AdamKeher/XCopyStandalone/esp8266/data/images/AK74.png

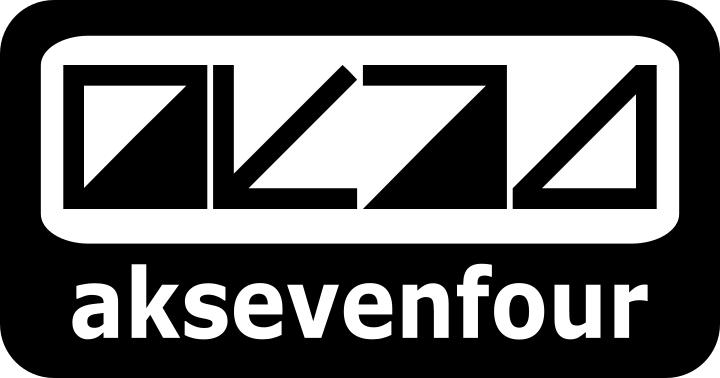
esp8266/data/images/AK74.png
