AdamKeher/XCopyStandalone/esp8266/data/images/AK74_white.png

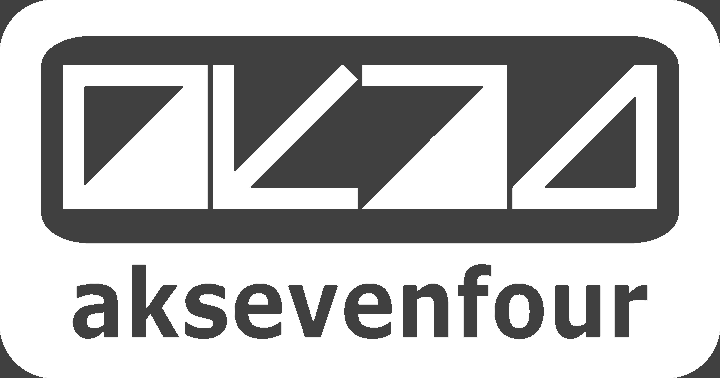
esp8266/data/images/AK74_white.png
