AdamKeher/XCopyStandalone/files/Graphics/mutation.bmp

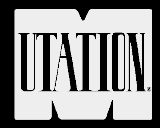
files/Graphics/mutation.bmp
