AdamKeher/XCopyStandalone/files/Graphics/sysinfo.bmp

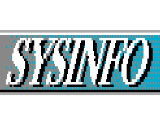
files/Graphics/sysinfo.bmp
