AdamKeher/XCopyStandalone/files/Graphics/XCopy Board.png

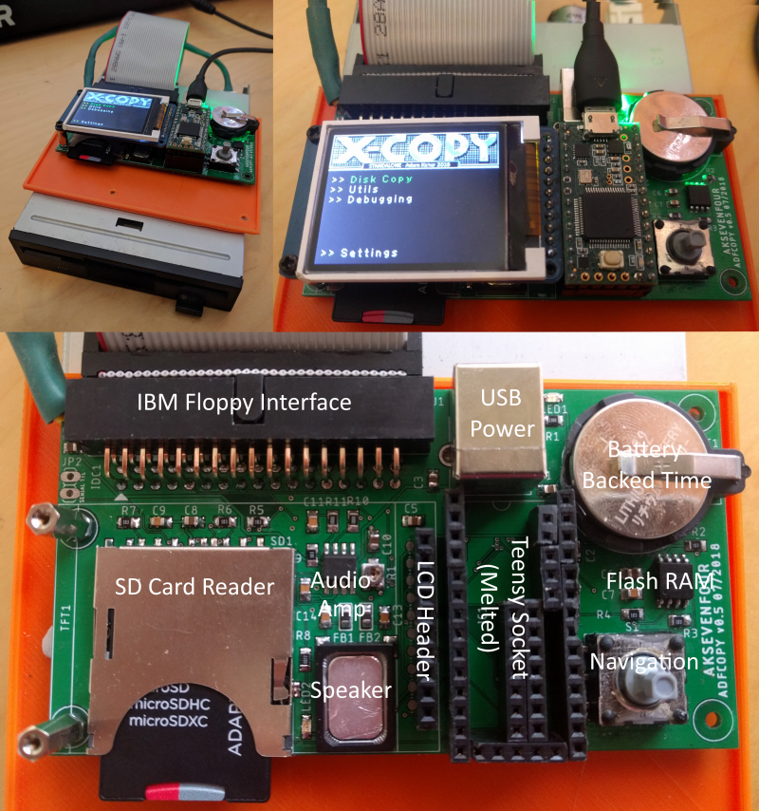
files/Graphics/XCopy Board.png
