AdamKeher/XCopyStandalone/src/XCopy/XCopyDisk.cpp

#include "XCopyDisk.h"
#include "XCopyScratch.h"

// #define XCOPY_DEBUG 1

/**
 * @brief Initialise the object
 * 
 * @param  graphics pointer to XCopyGraphics object
 * @param  audio pointer to XCopyAudio object
 * @param  esp pointer to XCopyESP object
 */
void XCopyDisk::begin(XCopyGraphics *graphics, XCopyAudio *audio, XCopyESP8266 *esp, XCopyFloppy *floppy)
{
    _graphics = graphics;
    _audio = audio;
    _esp = esp;
    _floppy = floppy;

    _floppy->setupDrive();

    // setupDrive() is what malloc's the track buffer, so the scratch arena cannot be
    // offered to anyone before this point. See XCopyScratch.h for why the buffer is
    // shared rather than each caller keeping its own.
    XCopyScratch::attach(_floppy);
}

// UI

/**
 * @brief Wait for user to change the disk in the current floppy drive. 
 */
void XCopyDisk::changeDisk()
{
    _graphics->clearScreen();
    _graphics->drawText(0, 60, ST7735_YELLOW, "           Change Disk");
    _esp->setStatus("Change Disk");

    bool diskInserted = _floppy->diskChange();
    while (diskInserted)
    {
        if (_cancelOperation)
        {
            _graphics->drawText(0, 70, ST7735_RED, "            Cancelled");
            return;
        }
        diskInserted = _floppy->diskChange();
        delay(500);
    }

    _graphics->drawText(0, 60, ST7735_GREEN, "    Disk Ejected. Waiting", true);
    _esp->setStatus("Disk Ejected. Waiting ...");

    diskInserted = _floppy->diskChange();
    while (!diskInserted)
    {
        if (_cancelOperation)
        {
            _graphics->drawText(0, 70, ST7735_RED, "            Cancelled");
            _esp->setStatus("Cancelled");
            return;
        }
        diskInserted = _floppy->diskChange();
        delay(3000);
    }
}

/**
 * @brief Draw disk flux on TFT and WebUI interfaces
 * 
 * @param trackNum track number of flux data
 * @param scale scale value flux values for drawing on TFT screen
 * @param yoffset y offset for drawing on TFT screen
 * @param updateWebUI bool value to determine if WebUI is updated
 */
void XCopyDisk::drawFlux(uint8_t trackNum, uint8_t scale, uint8_t yoffset, bool updateWebUI)
{
    // web interface
    // Static, and appended to in place below, so this buffer is allocated once
    // for the life of the program. Building it locally meant a ~1KB alloc/free
    // per track plus a realloc per concatenation, all inside the few KB left
    // between the stream buffer and the stack - which fragmented the heap until
    // the allocator wedged partway through the disk.
    static String data;
    data.reserve(1024);
    data.remove(0);
    for (int i = 0; i < 255; i++) {
        // concat() appends in place, so the reserve above holds. `data = data + x`
        // does not: it builds a StringSumHelper copy sized to len and assigns it
        // back, discarding the reserved capacity and reallocating every iteration.
        data.concat(_floppy->getHist()[i]);
        data.concat('|');
    }
    // Sent in pieces: concatenating these built another ~600 byte temporary
    // (plus intermediates) on top of the one we already hold, in the same
    // few KB left between the stream buffer and the stack.
    if (updateWebUI) {
        _esp->print("broadcast flux," + String(trackNum) + ",");
        _esp->print(data);
        _esp->print("\r\n");
    }

    // tft screen
    int scaled = 0;
    for (int i = 0; i < 255; i = i + scale)
    {
        // scale hist value
        for (int s = 0; s < scale; s++) { scaled += _floppy->getHist()[i + s]; }

        // draw hist
        if (scaled > 0)
        {
            scaled = (scaled / (32 * scale));
            scaled = scaled < 255 ? scaled : 255;
            float ratio = scaled / 255.0f;

            if (scaled < 5)
                _graphics->getTFT()->drawPixel(trackNum, yoffset, _graphics->LerpRGB(ST7735_WHITE, ST7735_YELLOW, ratio));
            else if (scaled < 50)
                _graphics->getTFT()->drawPixel(trackNum, yoffset, _graphics->LerpRGB(ST7735_YELLOW, ST7735_ORANGE, ratio));
            else
                _graphics->getTFT()->drawPixel(trackNum, yoffset, _graphics->LerpRGB(ST7735_ORANGE, ST7735_RED, ratio));
        }
        yoffset++;
    }
}

// File & Volume Names

/**
 * @brief Callback function used by SDfile::dateTimeCallback.
 *        Return today's date.
 * 
 * @param date date variable
 * @param time time variable
 */
void XCopyDisk::dateTime(uint16_t *date, uint16_t *time)
{
    // return date using FAT_DATE macro to format fields
    *date = FAT_DATE(year(), month(), day());

    // return time using FAT_TIME macro to format fields
    *time = FAT_TIME(hour(), minute(), second());
}

/**
 * @brief Get volume name of ADF file
 * 
 * @param ADFFileName path of ADF file
 * @param Source indicates SDCard or Flash Memory source
 * 
 * @result volume name for ADF file, "NDOS" if the disk is not dos formatted
 */
String XCopyDisk::getADFVolumeName(String ADFFileName, ADFFileSource source)
{
    _esp->setStatus("Geting Disk Name");

    String volumeName;
    volumeName = "NDOS";

    if (ADFFileName == "")
        return ">> File Error";

    // Zeroed: an unrecognised source would otherwise run the root block checks below
    // over stack garbage. All-zero fails them and yields "NDOS".
    byte trackBuffer[512];
    memset(trackBuffer, 0, sizeof(trackBuffer));

    if (source == _sdCard)
    {
        XCopySDCard _sdcard;

        // Was `if (_sdcard.begin())`, which reported an error when the card
        // initialised and carried on when it did not. begin() returns true on
        // success.
        if (!_sdcard.begin()) {
            return ">> SD Error";
        }

        File ADFFile;
        ADFFile.open(ADFFileName.c_str(), FILE_READ);

        if (!ADFFile) {
            return ">> File Error";
        }

        ADFFile.seek(40 * 2 * 11 * 512);
        ADFFile.read(trackBuffer, sizeof(trackBuffer));
        ADFFile.close();
    }
    else if (source == _flashMemory) {
        if (!SerialFlash.begin(PIN_FLASHCS)) { return ">> Flash Error"; }

        SerialFlashFile ADFFile = SerialFlash.open(ADFFileName.c_str());

        if (!ADFFile) { return ">> File Error"; }

        ADFFile.seek(40 * 2 * 11 * 512);
        ADFFile.read(trackBuffer, sizeof(trackBuffer));
        ADFFile.close();
    }

    int nameLen = trackBuffer[432];
    if (nameLen > 30) { return "NDOS"; }
    int temp = 0;
    for (int i = 0x04; i < 0x0c; i++) {
        temp += trackBuffer[i];
    }
    for (int i = 0x10; i < 0x14; i++) {
        temp += trackBuffer[i];
    }
    for (int i = 463; i < 472; i++) {
        temp += trackBuffer[i];
    }
    for (int i = 496; i < 504; i++) {
        temp += trackBuffer[i];
    }
    if (temp != 0) { return "NDOS"; }
    for (int i = 0; i < 4; i++) {
        temp += trackBuffer[i];
    }
    if (temp != 2) { return "NDOS"; }
    temp = 0;
    for (int i = 508; i < 512; i++) {
        temp += trackBuffer[i];
    }
    if (temp != 1) { return "NDOS"; }
    volumeName = "";
    for (int i = 0; i < nameLen; i++) {
        volumeName += (char)trackBuffer[433 + i];
    }

    return volumeName;
}

/**
 * @brief Generated ADF filename in format: /<SD_ADF_PATH>/<DATETIME> <DISKNAME>.adf
 * 
 * @param diskname diskname used in ADF filename
 * 
 * @result generated ADF file name
 */
String XCopyDisk::generateADFFileName(String diskname) {
    String path = String(SD_ADF_PATH);
    char dtBuffer[32];
    sprintf(dtBuffer, "%04d%02d%02d %02d%02d", year(), month(), day(), hour(), minute());
    String datetime = String(dtBuffer);
    return "/" + path + "/" + datetime + " " + diskname + ".adf";
}

// Cancel

/**
 * @brief Cancel running operation
 */
void XCopyDisk::cancelOperation() {
    _cancelOperation = true;
}

/**
 * @brief Used to update TFT and WebUI interface when operation is cancelled.
 *        If specificed, unprocessed tracks will be highlighted red.
 * 
 * @param trackNum logical track number operation was canceled on. -1 if not needed.
 */
void XCopyDisk::OperationCancelled(uint8_t trackNum) {
    _graphics->drawText(0, 10, ST7735_RED, "Operation Cancelled", true);
    if (trackNum >= 0)
    {
        _graphics->drawDisk(trackNum, ST7735_RED);
        _esp->sendWebSocket("resetTracks,red," + String(trackNum));
        _trackMap.setRange(trackNum, trackSkipped);
    }
    // Released before logging - anything printed while the map owns the console
    // scrolls the table out from under the cursor addressing.
    _trackMap.end("CANCELLED");
    Log << XCopyConsole::error("Operation Cancelled") << "\r\n";
    _audio->playBong(false);
}

// Read & Write tracks

/**
 * @brief Reads specified track into track buffer
 * 
 * @param trackNum logical track number to read
 * @param verify flags if this read is being use in a verify operation
 * @param retryCount number of retries when reading disk
 * @param silent output flag
 * 
 * @result number of retries required to read track. -1 is error. 
 */
int XCopyDisk::readDiskTrack(uint8_t trackNum, bool verify, uint8_t retryCount, bool silent) {
    // white = seek
    // green = OK - no retries
    // yellow = ~OK - quick retry required
    // orange = ~OK - retry required
    // red = ERROR - track did not read correctly
    // return 0 = OK, -1 = ERROR, >0 = OK w/ RETRY Count

    int retries = 0;
    int readResult = -1;

    while (readResult == -1 && retries < retryCount) {
        // read track
        if (!silent) _graphics->drawTrack(trackNum / 2, trackNum % 2, true, false, 0, verify, ST7735_WHITE);
        if (!silent) _trackMap.setTrack(trackNum, trackBusy, 0, verify);
        _esp->setTrack(trackNum, "white", verify ? "V" : "");
        _floppy->gotoLogicTrack(trackNum);
        readResult = _floppy->readTrack(true);

        if (readResult != -1) {
            // read OK
            if (_floppy->getWeakTrack() > 0) {
                if (!silent) _graphics->drawTrack(trackNum / 2, trackNum % 2, true, false, 0, verify, ST7735_YELLOW);
                if (!silent) _trackMap.setTrack(trackNum, trackWeak, 0, verify);
                _esp->setTrack(trackNum, "yellow", verify ? "V" : "");
            }
            else {
                if (!silent) _graphics->drawTrack(trackNum / 2, trackNum % 2, true, false, 0, verify, ST7735_GREEN);
                if (!silent) _trackMap.setTrack(trackNum, trackOK, 0, verify);
                _esp->setTrack(trackNum, "green", verify ? "V" : "");
            }
        }
        else {
            // read error
            if (!silent) _graphics->drawTrack(trackNum / 2, trackNum % 2, true, false, 0, verify, ST7735_RED);            
            if (!silent) _trackMap.setTrack(trackNum, trackError, retries + 1, verify);
            _esp->setTrack(trackNum, "red", verify ? "V" : String(retries + 1));
            retries++;
            _audio->playBong(false);
            delay(1000);
        }

        if (_cancelOperation) { return -1; }
    }

    if (readResult == 0 && retries > 0) {
        if (!silent) _graphics->drawTrack(trackNum / 2, trackNum % 2, true, false, 0, verify, ST7735_ORANGE);
        if (!silent) _trackMap.setTrack(trackNum, trackRetried, retries, verify);
        _esp->setTrack(trackNum, "orange", verify ? "V" : String(retries));
    }

    return readResult == -1 ? readResult : retries;
}

/**
 * @brief Write specified track from track buffer
 * 
 * @param trackNum logical track number to write
 * @param retryCount number of retries when writing track
 * 
 * @result number of retries required to write track. -1 is error. 
 */
int XCopyDisk::writeDiskTrack(uint8_t trackNum, uint8_t retryCount)
{
    // white = seek
    // green = OK
    // orange = ~OK - retry required
    // red = ERROR - track did not write correctly
    // return: 0+ = OK, -1 = ERROR

    int retries = 0;
    int writeResult = -1;

    while (writeResult == -1 && retries < retryCount) {
        // write track
        _graphics->drawTrack(trackNum / 2, trackNum % 2, true, false, 0, false, ST7735_WHITE);
        _trackMap.setTrack(trackNum, trackBusy);
        _esp->setTrack(trackNum, "white");
        _floppy->gotoLogicTrack(trackNum);    
        writeResult = _floppy->writeTrack(); // returns 0 = OK, -1 = ERROR

        if (writeResult == 0) {
            // write OK
            if (retries == 0) {
                // write OK w/ no retries
                _graphics->drawTrack(trackNum / 2, trackNum % 2, true, false, 0, false, ST7735_GREEN);
                _trackMap.setTrack(trackNum, trackOK);
                _esp->setTrack(trackNum, "green");
            }
            else {
                // write OK w/ retries
                _graphics->drawTrack(trackNum / 2, trackNum % 2, true, false, 0, false, ST7735_ORANGE);
                _trackMap.setTrack(trackNum, trackRetried, retries + 1);
                _esp->setTrack(trackNum, "orange", String(retries + 1));
            }
        }
        else {
            // write error
            _graphics->drawTrack(trackNum / 2, trackNum % 2, true, true, retries + 1, false, ST7735_RED);
            _trackMap.setTrack(trackNum, trackError, retries + 1);
            _esp->setTrack(trackNum, "red", String(retries + 1));
            // The map already carries the failing track and the attempt number;
            // printing here as well would scroll the table out from under it.
            if (!_trackMap.active()) Serial << "Write failed! - Try: " << retries + 1 << "\r\n";
            retries++;
            _audio->playBong(false);
            delay(1000);
        }        

        if (_cancelOperation) { return -1; }
    }

    return writeResult == -1 ? writeResult : retries;
}

// ADF Disk

/**
 * @brief Copy floppy disk to ADF file on SDCard or Flash
 * 
 * @param ADFFileName path of ADF file on SDCard, if blank and destination is SDCard, the name will be autogenerated
 * @param verify verify tracks by reading track a second time and compairing it to the data written
 * @param retryCount number of retries when reading track
 * @param destination indicates SDCard or Flash Memory destination
 * @param setEsp set mode and state for WebUI
 * 
 * @result success or failure of copy process
 * 
 * @todo TODO: Create XCopyLogFile object? Move CRC code into function. 
 */
bool XCopyDisk::diskToADF(String ADFFileName, bool verify, uint8_t retryCount, ADFFileSource destination, bool setEsp) {
    FastCRC32 CRC32;
    FastCRC16 CRC16;
    uint32_t disk_crc32 = 0;
    uint16_t track_crc16 = 0;
    _cancelOperation = false;
    String statusText = "";
    String diskName = "";

    int readErrors = 0;
    int weakTracks = 0;
    int totalReadErrors = 0;
    int totalWeakTracks = 0;
    
    File ADFFile;
    File ADFLogFile;
    SerialFlashFile ADFFlashFile;

    // setup TFT and WebUI
    _graphics->bmpDraw("XCPYLOGO.BMP", 0, 87);
    _graphics->drawDiskName("");
    _graphics->drawDisk();

    // dont update the mode and state for functions such as Disk to Disk
    if (setEsp) {
        _esp->setMode(destination == _sdCard ? "Copy Disk to ADF" : "Copy Disk to Flash");
        _esp->setState(destination == _sdCard ? copyDiskToADF : copyDiskToFlash);
    }
    _esp->resetDisk();
    _esp->setTab("diskcopy");

    // check if disk is present in floppy
    if (!_floppy->diskChange()) {
        _graphics->drawText(0, 10, ST7735_RED, "No Disk Inserted");
        Log << XCopyConsole::error("No Disk Inserted") << "\r\n";
        _esp->setStatus("No disk inserted");
        _audio->playBong(false);
        return false;
    }

    // get and set diskname
    diskName = _floppy->getName();
    _graphics->drawDiskName(diskName);
    _esp->setDiskName(diskName);

    // get filesnames
    String fullPath = ADFFileName == "" ? generateADFFileName(diskName) : ADFFileName;
    String logfileName = fullPath.substring(0, fullPath.length() - 4).append(".log");

    // set status on WebUI
    statusText = String("Copying floppy disk to ").append(destination == _sdCard ? "'"+ fullPath +"' on SD card" : "flash memory");   
    _esp->setStatus(statusText);

    // Open SD File or SerialFile
    XCopySDCard _sdcard;
    if (destination == _sdCard) {
        // card detect
        if (!_sdcard.cardDetect()) {
            _graphics->drawText(0, 10, ST7735_RED, "No SDCard detected");
            Log << XCopyConsole::error("No SDCard detected") << "\r\n";
            _esp->setStatus("SD card not inserted");
            _audio->playBong(false);
            return false;
        }

        // init
        if (!_sdcard.begin()) {
            _graphics->drawText(0, 10, ST7735_RED, "SD Init Failed");
            Log << XCopyConsole::error("SD Init Failed") << "\r\n";
            _esp->setStatus("SD card initialisation failed");
            _audio->playBong(false);
            return false;
        }

        // make ADF path
        if (!_sdcard.fileExists(SD_ADF_PATH)) _sdcard.makeDirectory(SD_ADF_PATH);

        // remove sdcard adf & log files if they exist
        if (_sdcard.fileExists(fullPath)) _sdcard.deleteFile(fullPath.c_str());
        if (_sdcard.fileExists(logfileName)) _sdcard.deleteFile(logfileName.c_str());

        // open sdcard files
        SdFile::dateTimeCallback(dateTime);
        ADFFile = _sdcard.getSdFat().open(fullPath.c_str(), FILE_WRITE);
        ADFLogFile = _sdcard.getSdFat().open(logfileName.c_str(), FILE_WRITE);
        SdFile::dateTimeCallbackCancel();

        // if adf file failed top open
        if (!ADFFile) {
            ADFFile.close();
            ADFLogFile.close();
            _graphics->drawText(0, 10, ST7735_RED, "SD ADF File Open Failed");
            Log << XCopyConsole::error("SD ADF File Open Failed") << "\r\n";
            _esp->setStatus("File '" + ADFFileName + "' failed to open on the SD card");
            _audio->playBong(false);
            return false;
        }

        // if log file failed to open
        if (!ADFLogFile) {
            ADFFile.close();
            ADFLogFile.close();
            _graphics->drawText(0, 10, ST7735_RED, "SD Log File Open Failed");
            Log << XCopyConsole::error("SD Log File Open Failed") << "\r\n";
            _esp->setStatus("File '" + logfileName + "' failed to open on the SD card");
            _audio->playBong(false);
            return false;
        }

        // create log file header
        ADFLogFile.println("{");
        ADFLogFile.println("\t\"volume\": \"" + diskName + "\",");
        char buffer[256];
        sprintf(buffer, "%04d-%02d-%02d %02d:%02d:%02d", year(), month(), day(), hour(), minute(), second());
        ADFLogFile.println("\t\"date\": \"" + String(buffer) + "\",");
        ADFLogFile.println("\t\"origin\": \"XCopy Standalone\",");
        ADFLogFile.println("\t\"timestamp\": " + String(now()) + ",");
        ADFLogFile.println("\t\"tracks\": [");
    }
    else if (destination == _flashMemory) {
        if (!SerialFlash.begin(PIN_FLASHCS)) {
            _graphics->drawText(0, 10, ST7735_RED, "Serial Flash Init Failed");
            Log << XCopyConsole::error("Serial Flash Init Failed") << "\r\n";
            _esp->setStatus("Onboard serial Flash failed to initialise");
            _audio->playBong(false);
            return false;
        }

        ADFFlashFile = SerialFlash.open(ADFFileName.c_str());

        _graphics->drawText(0, 10, ST7735_ORANGE, "Erasing Flash...", true);
        _esp->setStatus("Erasing Flash ...");

        ADFFlashFile.erase();

        while (!SerialFlash.ready()) { }

        _graphics->drawText("Done");
        _esp->setStatus("Erasing Flash ... Done");

        ADFFlashFile = SerialFlash.open(ADFFileName.c_str());
        if (!ADFFlashFile) {
            ADFFlashFile.close();
            _graphics->drawText(0, 10, ST7735_RED, "Serial Flash File Open Failed", true);
            Log << XCopyConsole::error("Serial Flash File Open Failed") << "\r\n";
            _esp->setStatus("Serial flash file failed to open");
            _audio->playBong(false);
            return false;
        }

        ADFFlashFile.seek(0);
    }

    // clear XCopy logo for flux
    _graphics->getTFT()->fillRect(0, 85, _graphics->getTFT()->width(), _graphics->getTFT()->height()-85, ST7735_BLACK);
    _graphics->getTFT()->drawFastHLine(0, 85, _graphics->getTFT()->width(), ST7735_GREEN);

    _trackMap.begin(destination == _sdCard ? "READ DISK TO ADF" : "READ DISK TO FLASH", diskName);

    // MD5 setup
    MD5_CTX ctx;
    MD5::MD5Init(&ctx);

    // YELLOW = Begin, GREEN = Read OK, ORANGE = Read after Retries, RED = Read Error, MAGENTA = Verify Error
    for (int trackNum = 0; trackNum < 160; trackNum++) {
        if (_cancelOperation) {
            OperationCancelled(trackNum);
            ADFLogFile.println("\r\nCancelled.");
            ADFLogFile.close();
            ADFFile.close();
            return false;
        }

        // read track
        int readResult = readDiskTrack(trackNum, false, retryCount);

        // draw flux
        _floppy->analyseHist(true);
        drawFlux(trackNum, 6, 85);

        if (_floppy->getWeakTrack()) {
            weakTracks += _floppy->getWeakTrack();
            totalWeakTracks++;
        }

        if (readResult != 0) {
            // if there has been error on either side, set error for whole cylinder else increment retry count
            if (readErrors == -1 || readResult == -1)
                readErrors = -1;
            else
                readErrors += readResult;
            totalReadErrors++;
        }

        // calculate CRC
        if (destination == _sdCard) {
            uint8_t side = trackNum % 2;

            for (int sec = 0; sec < 11; sec++) {
                struct Sector *aSec = (Sector *)&_floppy->getTrack()[sec].sector;

                // total disk CRC
                if (sec == 0 && trackNum == 0)
                    disk_crc32 = CRC32.crc32(aSec->data, sizeof(aSec->data));
                else
                    disk_crc32 = CRC32.crc32_upd(aSec->data, sizeof(aSec->data));

                // cyl CRC16
                if (sec == 0 && side == 0) {
                    // Serial << "trackNum: " << trackNum << " Side: " << side << " Sec: " << sec << " CCITT\r\n";
                    track_crc16 = CRC16.ccitt(aSec->data, sizeof(aSec->data));
                }
                else {
                    // Serial << "trackNum: " << trackNum << " Side: " << side << " Sec: " << sec << " CCITT_UPD\r\n";
                    track_crc16 = CRC16.ccitt_upd(aSec->data, sizeof(aSec->data));
                }
            }

            if (side == 1) {
                uint8_t cylinder = (trackNum - 1) / 2;
                ADFLogFile.print("\t\t{ \"track\": " + String(cylinder) + ", \"crc16\": \"0x");
                ADFLogFile.print(track_crc16, HEX);
                ADFLogFile.print("\", \"retries\": " + String(readErrors) + ", \"weak\": " + String(weakTracks) + " }");
                ADFLogFile.println(cylinder != 79 ? "," : "");

                weakTracks = 0;
                readErrors = 0;
            }
        }

        // write track (11 sectors per track)
        for (int i = 0; i < 11; i++) {
            const struct Sector *aSec = (Sector *)&_floppy->getTrack()[i].sector;
            // calculate MD5
            MD5::MD5Update(&ctx, aSec->data, 512);
            if (destination == _sdCard) {
                ADFFile.write(aSec->data, 512);
            }
            else if (destination == _flashMemory) {
                ADFFlashFile.write(aSec->data, 512);
                ADFFlashFile.flush();
                while (!SerialFlash.ready()) { }
            }
        }

        // verify
        if (verify) {
            // reread track to compare to file
            readDiskTrack(trackNum, true, retryCount);

            bool compareError = false;
            char buffer[512];

            // move file pointer pack 1 track
            if (destination == _sdCard)
                ADFFile.seek(ADFFile.position() - 11 * 512);
            else if (destination == _flashMemory)
                ADFFlashFile.seek(ADFFlashFile.position() - 11 * 512);

            // compare sectors to file
            for (int i = 0; i < 11; i++) {
                const struct Sector *aSec = (Sector *)&_floppy->getTrack()[i].sector;

                if (destination == _sdCard)
                    ADFFile.read(buffer, sizeof(buffer));
                else if (destination == _flashMemory)
                    ADFFlashFile.read(buffer, sizeof(buffer));

                if (memcmp(aSec->data, buffer, 512))
                    compareError = true;
            }

            if (compareError) {
                _graphics->drawTrack(trackNum / 2, trackNum % 2, true, false, 0, true, ST7735_MAGENTA);
                _trackMap.setTrack(trackNum, trackVerifyError, 0, true);
                _esp->setTrack(trackNum, "magenta,");
                _audio->playBong(false);
            }
            else {
                _graphics->drawTrack(trackNum / 2, trackNum % 2, true, false, 0, true, ST7735_GREEN);
                _trackMap.setTrack(trackNum, trackOK, 0, true);
                _esp->setTrack(trackNum, "green");
            }
        }
    }

    String sMD5 = ctxToMD5(&ctx);

    _trackMap.end(String("COMPLETE - ") + totalReadErrors + " bad, " + totalWeakTracks + " weak of 160 tracks");
    Log << (totalReadErrors ? XCopyConsole::error("Read errors on " + String(totalReadErrors) + " track(s)")
                            : XCopyConsole::success("All 160 tracks read")) << "\r\n";
    Log << "MD5: " << sMD5 << "\r\n";

    if (destination == _sdCard) {
        ADFLogFile.println("\t],");
        ADFLogFile.println("\t\"readErrors\": " + String(totalReadErrors) + ",");
        ADFLogFile.println("\t\"weakTracks\": " + String(totalWeakTracks) + ",");
        ADFLogFile.print("\t\"crc32\": \"0x");
        ADFLogFile.print(disk_crc32, HEX);
        ADFLogFile.println("\",");
        ADFLogFile.println("\t\"md5\": \"" + sMD5 + "\"");
        ADFLogFile.println("}");
    }

    ADFFile.close();
    ADFLogFile.close();
    ADFFlashFile.close();
    _audio->playBoing(false);

    statusText = String("Completed copying floppy disk to ").append(destination == _sdCard ? "'<a href=\"/sdcard" + fullPath + "\">" + fullPath + "</a>' on SD card. <a target=\"_blank\" href=\"/sdcard" + logfileName  + "\">Log File</a> <i class=\"fa-solid fa-hashtag\"></i> MD5: " + sMD5 : "flash memory. <i class=\"fa-solid fa-hashtag\"></i> MD5: " + sMD5);
    _esp->setStatus(statusText);

    return true;
}

/**
 * @brief Generated SCP filename in format: /<SD_SCP_PATH>/<DATETIME> <DISKNAME>.scp
 *
 * @param diskname diskname used in SCP filename
 *
 * @result generated SCP file name
 */
String XCopyDisk::generateSCPFileName(String diskname) {
    String path = String(SD_SCP_PATH);
    char dtBuffer[32];
    sprintf(dtBuffer, "%04d%02d%02d %02d%02d", year(), month(), day(), hour(), minute());
    String datetime = String(dtBuffer);
    return "/" + path + "/" + datetime + " " + diskname + ".scp";
}

/**
 * @brief Captures one track of raw flux and streams it into an open SCP image.
 *
 * The counterpart of readDiskTrack() for flux, and it paints the same three surfaces
 * in the same order with the same colours. What it does not have is a notion of a
 * good or a bad read: there is nothing to checksum, so the only failure a capture can
 * detect is the SD card falling behind the drive, which fluxOverran() reports and a
 * retry fixes.
 *
 * @param trackNum logical track number, which is also the SCP track number
 * @param writer image to stream into, already positioned by the caller
 * @param revolutions revolutions to store
 * @param retryCount retries allowed before the track is abandoned
 *
 * @result number of retries required. -1 is error.
 */
int XCopyDisk::captureDiskTrack(uint8_t trackNum, XCopySCPWriter *writer,
                                uint8_t revolutions, uint8_t retryCount) {
    int retries = 0;

    // Held for the whole track, retries included, and released however this returns.
    // The ring is the MFM stream buffer; nothing may decode a track or run a transfer
    // until it is given back.
    XCopyScratch::Guard scratch("disk.captureDiskTrack", sizeof(uint16_t));
    if (!scratch.valid()) return -1;

    // A revolution is 200ms; the drive may need to spin up and the first index can be
    // a full revolution away. Generous, because the alternative to a timeout here is
    // hanging forever on a drive with no disk in it.
    const uint32_t captureTimeout = 2000 + ((uint32_t)revolutions * 400);

    while (retries <= retryCount) {
        _graphics->drawTrack(trackNum / 2, trackNum % 2, true, retries > 0, retries, false, ST7735_WHITE);
        _trackMap.setTrack(trackNum, trackBusy);
        _esp->setTrack(trackNum, "white", retries > 0 ? String(retries) : "");

        _floppy->gotoLogicTrack(trackNum);

        if (!writer->beginTrack(trackNum)) return -1;

        // The capture ring is the MFM stream buffer, claimed by the guard above. It is
        // the only block of RAM big enough to ride out an SD write stall.
        uint16_t *ring = (uint16_t *)scratch.get();
        size_t ringSamples = XCopyScratch::capacity() / sizeof(uint16_t);

        if (!_floppy->beginFluxCapture(ring, ringSamples, revolutions)) {
            writer->abortTrack();
            return -1;
        }

        bool ok = writer->beginRevolution();
        uint8_t rev = 0;
        uint32_t drained = 0;   // raw samples handed to the writer
        uint32_t revStart = 0;  // drained at the start of the revolution in progress
        uint32_t boundary = 0;  // drained value that ends it, once the ISR knows
        bool haveBoundary = false;
        bool overran = false;
        bool incomplete = false;
        uint32_t started = millis();

        while (ok && rev < revolutions) {
            if (_cancelOperation) break;

            if (_floppy->fluxOverran()) { overran = true; break; }

            if (millis() - started > captureTimeout) { incomplete = true; break; }

            // The boundary of the revolution being written becomes knowable the
            // moment the ISR closes it, and it always closes it before storing a
            // sample beyond it - so a boundary can never be missed by draining past.
            if (!haveBoundary && _floppy->fluxRevolutionsCaptured() > rev) {
                boundary = revStart + _floppy->fluxRevolutionSamples(rev);
                haveBoundary = true;
            }

            const uint16_t *samples;
            size_t avail = _floppy->fluxPeek(&samples);

            if (avail == 0) {
                // nothing left and nothing more coming: the capture ended early
                if (_floppy->fluxCaptureDone() && !haveBoundary) { incomplete = true; break; }
                continue;
            }

            size_t take = avail;
            if (haveBoundary && (drained + take) > boundary) take = boundary - drained;

            if (take > 0) {
                ok = writer->writeFlux(samples, take);
                _floppy->fluxConsume(take);
                drained += take;
            }

            if (haveBoundary && drained == boundary) {
                ok = ok && writer->endRevolution(_floppy->fluxRevolutionTicks(rev));
                rev++;
                revStart = boundary;
                haveBoundary = false;
                if (rev < revolutions) ok = ok && writer->beginRevolution();
            }
        }

        _floppy->endFluxCapture();

        // Rewind before leaving, so a cancelled track does not strand its
        // placeholder header in the image - beginTrack() wrote one, and only
        // endTrack() or abortTrack() accounts for it.
        if (_cancelOperation) {
            writer->abortTrack();
            return -1;
        }

        if (ok && !overran && !incomplete && rev == revolutions) {
            if (!writer->endTrack()) return -1;

            if (retries > 0) {
                _graphics->drawTrack(trackNum / 2, trackNum % 2, true, false, 0, false, ST7735_ORANGE);
                _trackMap.setTrack(trackNum, trackRetried, retries);
                _esp->setTrack(trackNum, "orange", String(retries));
            }
            else {
                _graphics->drawTrack(trackNum / 2, trackNum % 2, true, false, 0, false, ST7735_GREEN);
                _trackMap.setTrack(trackNum, trackOK);
                _esp->setTrack(trackNum, "green");
            }
            return retries;
        }

        if (writer->failed()) return -1;

        // Rewind before retrying, so the partial capture is overwritten rather than
        // left in the image as unreferenced dead weight.
        if (!writer->abortTrack()) return -1;

        retries++;
        _graphics->drawTrack(trackNum / 2, trackNum % 2, true, true, retries, false, ST7735_RED);
        _trackMap.setTrack(trackNum, trackError, retries);
        _esp->setTrack(trackNum, "red", String(retries));
        _audio->playBong(false);
    }

    return -1;
}

/**
 * @brief Reads a floppy disk to a SuperCard Pro flux image on the SD card.
 *
 * Unlike diskToADF() this decodes nothing. Every flux transition the drive reports is
 * written out as it arrives, which is the whole point: copy protection, custom track
 * formats, long tracks and weak bits are exactly the things an ADF cannot represent,
 * and they are all still here.
 *
 * @param SCPFileName path of the SCP file on the SD card, or "" to generate one
 * @param revolutions revolutions stored per track, 1..SCP_MAX_REVS
 * @param startCylinder first cylinder to capture
 * @param endCylinder last cylinder to capture, inclusive. May exceed ADF_CYLINDERS -
 *        the extra cylinders are where out of band protections hide - but few drives
 *        reach MAX_CYLINDERS and none are obliged to.
 * @param retryCount retries per track before it is abandoned
 * @param setEsp set mode and state for WebUI
 */
bool XCopyDisk::diskToSCP(String SCPFileName, uint8_t revolutions, uint8_t startCylinder,
                          uint8_t endCylinder, uint8_t retryCount, bool setEsp) {
    _cancelOperation = false;
    String statusText = "";
    String diskName = "";
    int badTracks = 0;
    int retriedTracks = 0;

    File SCPFile;
    File SCPLogFile;
    XCopySCPWriter writer;

    if (revolutions < 1) revolutions = 1;
    if (revolutions > SCP_MAX_REVS) revolutions = SCP_MAX_REVS;
    if (endCylinder >= MAX_CYLINDERS) endCylinder = MAX_CYLINDERS - 1;
    if (startCylinder > endCylinder) startCylinder = endCylinder;

    const uint8_t startTrack = startCylinder * 2;
    const uint8_t endTrack = (endCylinder * 2) + 1;
    const uint8_t trackCount = endTrack - startTrack + 1;

    // setup TFT and WebUI
    _graphics->bmpDraw("XCPYLOGO.BMP", 0, 87);
    _graphics->drawDiskName("");
    _graphics->drawDisk();

    if (setEsp) {
        _esp->setMode("Copy Disk to SCP");
        _esp->setState(copyDiskToSCP);
    }
    _esp->resetDisk();
    _esp->setTab("diskcopy");

    if (!_floppy->diskChange()) {
        _graphics->drawText(0, 10, ST7735_RED, "No Disk Inserted");
        Log << XCopyConsole::error("No Disk Inserted") << "\r\n";
        _esp->setStatus("No disk inserted");
        _audio->playBong(false);
        return false;
    }

    /*
       The volume name is read through the normal MFM path, before any flux capture
       starts. It is only ever a label for the file, so a disk that cannot be decoded -
       which is most of what this feature exists for - falls back to a generic name
       rather than refusing to be imaged.
    */
    diskName = _floppy->getName();
    diskName.trim();
    if (diskName == "") diskName = "Unnamed";
    _graphics->drawDiskName(diskName);
    _esp->setDiskName(diskName);

    String fullPath = SCPFileName == "" ? generateSCPFileName(diskName) : SCPFileName;
    String logfileName = fullPath.substring(0, fullPath.length() - 4).append(".log");

    statusText = String("Capturing floppy disk flux to '") + fullPath + "' on SD card";
    _esp->setStatus(statusText);

    XCopySDCard _sdcard;

    if (!_sdcard.cardDetect()) {
        _graphics->drawText(0, 10, ST7735_RED, "No SDCard detected");
        Log << XCopyConsole::error("No SDCard detected") << "\r\n";
        _esp->setStatus("SD card not inserted");
        _audio->playBong(false);
        return false;
    }

    if (!_sdcard.begin()) {
        _graphics->drawText(0, 10, ST7735_RED, "SD Init Failed");
        Log << XCopyConsole::error("SD Init Failed") << "\r\n";
        _esp->setStatus("SD card initialisation failed");
        _audio->playBong(false);
        return false;
    }

    if (!_sdcard.fileExists(SD_SCP_PATH)) _sdcard.makeDirectory(SD_SCP_PATH);

    if (_sdcard.fileExists(fullPath)) _sdcard.deleteFile(fullPath.c_str());
    if (_sdcard.fileExists(logfileName)) _sdcard.deleteFile(logfileName.c_str());

    SdFile::dateTimeCallback(dateTime);
    SCPFile = _sdcard.getSdFat().open(fullPath.c_str(), FILE_WRITE);
    SCPLogFile = _sdcard.getSdFat().open(logfileName.c_str(), FILE_WRITE);
    SdFile::dateTimeCallbackCancel();

    if (!SCPFile) {
        SCPFile.close();
        SCPLogFile.close();
        _graphics->drawText(0, 10, ST7735_RED, "SD SCP File Open Failed");
        Log << XCopyConsole::error("SD SCP File Open Failed") << "\r\n";
        _esp->setStatus("File '" + fullPath + "' failed to open on the SD card");
        _audio->playBong(false);
        return false;
    }

    if (!SCPLogFile) {
        SCPFile.close();
        SCPLogFile.close();
        _graphics->drawText(0, 10, ST7735_RED, "SD Log File Open Failed");
        Log << XCopyConsole::error("SD Log File Open Failed") << "\r\n";
        _esp->setStatus("File '" + logfileName + "' failed to open on the SD card");
        _audio->playBong(false);
        return false;
    }

    /*
       SCP capture runs at DD timings. Amiga 3.5" disks are DD, and the HD prescaler
       halves the tick and so doubles the sustained SD write to around 754KB/s, which
       has not been measured on this hardware. XCopySCPWriter already converts either,
       so enabling HD here is a one line change once the throughput is known.
    */
    _floppy->setAutoDensity(false);
    _floppy->setMode(DD);
    const bool hd = false;

    if (!writer.begin(&SCPFile, startTrack, endTrack, revolutions, hd)) {
        SCPFile.close();
        SCPLogFile.close();
        _graphics->drawText(0, 10, ST7735_RED, "SCP Header Write Failed");
        Log << XCopyConsole::error("SCP Header Write Failed") << "\r\n";
        _esp->setStatus("Could not start the SCP image");
        _audio->playBong(false);
        return false;
    }

    SCPLogFile.println("{");
    SCPLogFile.println("\t\"volume\": \"" + diskName + "\",");
    char buffer[256];
    sprintf(buffer, "%04d-%02d-%02d %02d:%02d:%02d", year(), month(), day(), hour(), minute(), second());
    SCPLogFile.println("\t\"date\": \"" + String(buffer) + "\",");
    SCPLogFile.println("\t\"origin\": \"XCopy Standalone\",");
    SCPLogFile.println("\t\"format\": \"scp\",");
    SCPLogFile.println("\t\"revolutions\": " + String(revolutions) + ",");
    SCPLogFile.println("\t\"startTrack\": " + String(startTrack) + ",");
    SCPLogFile.println("\t\"endTrack\": " + String(endTrack) + ",");
    SCPLogFile.println("\t\"timestamp\": " + String(now()) + ",");
    SCPLogFile.println("\t\"tracks\": [");

    // clear XCopy logo for flux
    _graphics->getTFT()->fillRect(0, 85, _graphics->getTFT()->width(), _graphics->getTFT()->height()-85, ST7735_BLACK);
    _graphics->getTFT()->drawFastHLine(0, 85, _graphics->getTFT()->width(), ST7735_GREEN);

    _trackMap.begin("READ DISK TO SCP", diskName);

    _floppy->motorOn();
    _floppy->seek0();
    delay(100);

    for (int trackNum = startTrack; trackNum <= endTrack; trackNum++) {
        if (_cancelOperation) {
            OperationCancelled(trackNum);

            // Finish the image rather than abandoning it. Every track captured so
            // far is complete and referenced by the offset table, so end() turns
            // what is already on the card into a valid SCP of a partial disk.
            writer.end();

            // Closed off properly so the partial log is still parseable JSON.
            SCPLogFile.println("");
            SCPLogFile.println("\t],");
            SCPLogFile.println("\t\"cancelled\": true");
            SCPLogFile.println("}");
            SCPLogFile.close();
            SCPFile.close();
            return false;
        }

        int result = captureDiskTrack(trackNum, &writer, revolutions, retryCount);

        // the capture ISR keeps the histogram fed, so this draws the same as a read
        _floppy->analyseHist(true);
        drawFlux(trackNum, 6, 85);

        if (result < 0) badTracks++;
        else if (result > 0) retriedTracks++;

        // One entry per track, not per cylinder as the ADF log does: a flux capture
        // has no per-cylinder quantity to report, and the two sides can differ.
        // The separator leads rather than trails, so the array stays valid JSON.
        SCPLogFile.print(trackNum == startTrack ? "\t\t" : ",\r\n\t\t");
        SCPLogFile.print("{ \"track\": " + String(trackNum));
        SCPLogFile.print(", \"cylinder\": " + String(trackNum / 2));
        SCPLogFile.print(", \"side\": " + String(trackNum % 2));
        SCPLogFile.print(", \"bytes\": " + String(writer.trackBytes()));
        SCPLogFile.print(", \"retries\": " + String(result < 0 ? retryCount : result));
        SCPLogFile.print(", \"captured\": " + String(result < 0 ? "false" : "true") + " }");

        if (writer.failed()) {
            _trackMap.end("FAILED - SD card write error");
            Log << XCopyConsole::error("SD card write failed - the image is incomplete") << "\r\n";
            _esp->setStatus("SD card write failed, the image is incomplete");
            SCPLogFile.println("");
            SCPLogFile.println("\t],");
            SCPLogFile.println("\t\"writeFailed\": true");
            SCPLogFile.println("}");
            SCPLogFile.close();
            SCPFile.close();
            _audio->playBong(false);
            return false;
        }
    }

    bool finished = writer.end();

    _trackMap.end(String("COMPLETE - ") + badTracks + " bad, " + retriedTracks +
                  " retried of " + trackCount + " tracks");
    Log << (badTracks ? XCopyConsole::error("Capture errors on " + String(badTracks) + " track(s)")
                      : XCopyConsole::success("All " + String(trackCount) + " tracks captured")) << "\r\n";
    Log << "Revolutions: " << revolutions << "  Cylinders: " << startCylinder << "-" << endCylinder << "\r\n";

    SCPLogFile.println("");
    SCPLogFile.println("\t],");
    SCPLogFile.println("\t\"badTracks\": " + String(badTracks) + ",");
    SCPLogFile.println("\t\"retriedTracks\": " + String(retriedTracks) + ",");
    SCPLogFile.println("\t\"complete\": " + String(finished ? "true" : "false"));
    SCPLogFile.println("}");

    SCPFile.close();
    SCPLogFile.close();
    _audio->playBoing(false);

    statusText = String("Completed capturing floppy disk flux to '<a href=\"/sdcard") + fullPath +
                 "\">" + fullPath + "</a>' on SD card. <a target=\"_blank\" href=\"/sdcard" +
                 logfileName + "\">Log File</a>";
    _esp->setStatus(statusText);

    return finished;
}

/**
 * @brief Write ADF file to floppy disk from ADF file on SDCard or Flash
 * 
 * @param ADFFileName path of ADF file on SDCard
 * @param verify verify tracks by reading track a second time and compairing it to the data written
 * @param retryCount number of retries when writing track
 * @param destination indicates SDCard or Flash Memory source
 * @param setEsp set mode and state for WebUI
 * 
 * @todo TODO: Create XCopyLogFile object? Move CRC code into function. 
 */
void XCopyDisk::adfToDisk(String ADFFileName, bool verify, uint8_t retryCount, ADFFileSource source, bool setEsp) {
    if (source == _flashMemory) {
        // flash memory
        if (setEsp) {
            _esp->setMode(ADFFileName == "BLANK.TMP" ? "Format Disk" : "Copy Flash to Disk");
            _esp->setState(copyFlashToDisk);
        }
        _esp->setStatus("Copying disk from flash memory to floppy disk");
    }
    else {
        // sdcard
        if (setEsp) {
            _esp->setMode("Copy ADF to Disk");
            _esp->setState(copyADFToDisk);
        }
        _esp->setStatus("Copying ADF '" + ADFFileName + "' from SD card to floppy disk");
    }
    _esp->setTab("diskcopy");
    
    _cancelOperation = false;

    if (ADFFileName == "") { return; }

    _graphics->clearScreen();
    _graphics->bmpDraw("XCPYLOGO.BMP", 0, 87);
    _graphics->drawDiskName(ADFFileName.substring(ADFFileName.lastIndexOf("/") + 1));
    _graphics->drawDisk();

    _esp->resetDisk();

    if (!_floppy->diskChange()) {
        _graphics->drawText(0, 10, ST7735_RED, "No Disk Inserted");
        Log << XCopyConsole::error("No Disk Inserted") << "\r\n";
        _esp->setStatus("No Disk Inserted");
        _audio->playBong(false);
        return;
    }

    if (_floppy->getWriteProtect()) {
        _graphics->drawText(0, 10, ST7735_RED, "Disk Write Protected");
        Log << XCopyConsole::error("Disk Write Protected") << "\r\n";
        _esp->setStatus("Disk Write Protected");
        _audio->playBong(false);
        return;
    }

    File ADFFile;
    SerialFlashFile ADFFlashFile;
    XCopySDCard _sdcard;

    if (source == _sdCard) {
        if (!_sdcard.begin()) {
            _graphics->drawText(0, 10, ST7735_RED, "SD Init Failed");
            Log << XCopyConsole::error("SD Init Failed") << "\r\n";
            _esp->setStatus("SD Init Failed");
            _audio->playBong(false);
            return;
        }

        ADFFile = _sdcard.getSdFat().open(ADFFileName.c_str(), FILE_READ);
        if (!ADFFile) {
            _graphics->drawText(0, 10, ST7735_RED, "SD File Open Failed");
            Log << XCopyConsole::error("SD File Open Failed") << "\r\n";
            _esp->setStatus("SD File Open Failed");
            _audio->playBong(false);
            ADFFile.close();
            return;
        }
    }
    else if (source == _flashMemory) {
        if (!SerialFlash.begin(PIN_FLASHCS)) {
            _graphics->drawText(0, 10, ST7735_RED, "Serial Flash Init Failed");
            Log << XCopyConsole::error("Serial Flash Init Failed") << "\r\n";
            _esp->setStatus("Serial Flash Init Failed");
            _audio->playBong(false);
            return;
        }

        ADFFlashFile = SerialFlash.open(ADFFileName.c_str());
        if (!ADFFlashFile) {
            _graphics->drawText(0, 10, ST7735_RED, "Serial Flash File Open Failed");
            Log << XCopyConsole::error("Serial Flash File Open Failed") << "\r\n";
            _esp->setStatus("Serial Flash File Open Failed");
            _audio->playBong(false);
            ADFFlashFile.close();
            return;
        }

        ADFFlashFile.seek(0);
    }

    _floppy->setAutoDensity(false);
    _floppy->setMode(DD); // DD
    delay(5);
    _floppy->setCurrentTrack(-1);

    _floppy->motorOn();
    _floppy->seek0();
    delay(100);

    _trackMap.begin(source == _sdCard ? "WRITE ADF TO DISK" : "WRITE FLASH TO DISK",
                    ADFFileName.substring(ADFFileName.lastIndexOf("/") + 1));

    // MD5 setup
    MD5_CTX ctx;
    MD5::MD5Init(&ctx);

    // write ADF file
    for (int trackNum = 0; trackNum < 160; trackNum++) {
        if (_cancelOperation) {
            OperationCancelled(trackNum);
            return;
        }

        // read track from ADF file into track buffer
        for (int i = 0; i < 11; i++) {
            byte buffer[512];

            if (source == _sdCard)
                ADFFile.read(buffer, sizeof(buffer));
            else if (source == _flashMemory)
                ADFFlashFile.read(buffer, sizeof(buffer));

            struct Sector *aSec = (Sector *)&_floppy->getTrack()[i].sector[0];

            memcpy(aSec->data, buffer, 512);
        }

        // encode track
        _floppy->floppyTrackMfmEncode(trackNum, (byte *)_floppy->getTrack(), _floppy->getStream());

        // write track
        int result = writeDiskTrack(trackNum, retryCount);

        // verify track
        if (result != -1 && verify) {
            // read track
            readDiskTrack(trackNum, true, retryCount);

            bool compareError = false;
            byte buffer[512];

            // move file pointer pack 1 track
            if (source == _sdCard)
                ADFFile.seek(trackNum * 11 * 512);
            else if (source == _flashMemory)
                ADFFlashFile.seek(trackNum * 11 * 512);

            // compare sectors to file
            for (int i = 0; i < 11; i++) {
                if (source == _sdCard)
                    ADFFile.read(buffer, sizeof(buffer));
                else if (source == _flashMemory)
                    ADFFlashFile.read(buffer, sizeof(buffer));

                struct Sector *aSec = (Sector *)&_floppy->getTrack()[i].sector[0];

                if (memcmp(aSec->data, buffer, 512))
                    compareError = true;

                // calculate MD5
                MD5::MD5Update(&ctx, aSec->data, 512);
            }

            if (compareError) {
                _graphics->drawTrack(trackNum / 2, trackNum % 2, true, false, 0, false, ST7735_MAGENTA);
                _trackMap.setTrack(trackNum, trackVerifyError, 0, true);
                _esp->setTrack(trackNum, "magenta");
                _audio->playBong(false);
            }
            else {
                if (result == 0) {
                    // write OK w/ no retries
                    _graphics->drawTrack(trackNum / 2, trackNum % 2, true, false, 0, false, ST7735_GREEN);
                    _trackMap.setTrack(trackNum, trackOK, 0, true);
                    _esp->setTrack(trackNum, "green");
                }
                else {
                    // write OK w/ retries
                    _graphics->drawTrack(trackNum / 2, trackNum % 2, true, false, 0, false, ST7735_ORANGE);
                    _trackMap.setTrack(trackNum, trackRetried, result + 1, true);
                    _esp->setTrack(trackNum, "orange", String(result + 1));
                }
            }
        }
    }

    String status = "'" + ADFFileName + "' file written to disk";

    _trackMap.end("COMPLETE - 160 tracks written");
    Log << XCopyConsole::success(status) << "\r\n";

    if (verify) {
        // output MD5
        String sMD5 = ctxToMD5(&ctx);
        Log << "Verify data MD5: " << sMD5 << "\r\n";
        status.append(". Verify data <i class=\"fa-solid fa-hashtag\"></i> MD5: ").append(sMD5);
    }

    ADFFile.close();
    ADFFlashFile.close();
    _audio->playBoing(false);

    _esp->setStatus(status);
}

/**
 * @brief Copy Floppy disk to temporay flash and write back to Floppy Disk
 * 
 * @param verify verify tracks by reading track a second time and compairing it to the data written
 * @param retryCount number of retries when writing track
 */
void XCopyDisk::diskToDisk(bool verify, uint8_t retryCount) {
    _esp->setTab("diskcopy");
    _esp->setMode("Copy Disk to Disk");
    _esp->setStatus("Copying Disk to Disk");
    _esp->setState(copyDiskToDisk);

    _cancelOperation = false;
    _graphics->clearScreen();

    if (!_floppy->diskChange()) {
        _graphics->bmpDraw("XCPYLOGO.BMP", 0, 87);
        _graphics->drawDiskName("");
        _graphics->drawDisk();
        _graphics->drawText(0, 10, ST7735_RED, "No Disk Inserted");
        Log << XCopyConsole::error("No Disk Inserted") << "\r\n";
        _esp->setStatus("No Disk Inserted");
        _audio->playBong(false);
        return;
    }

    bool completed = diskToADF("DISKCOPY.TMP", verify, retryCount, _flashMemory, false);

    if (_cancelOperation || !completed) { return; }

    changeDisk();

    if (_cancelOperation) { return; }

    adfToDisk("DISKCOPY.TMP", verify, retryCount, _flashMemory, false);
}

/**
 * @brief Draw fullscreen TFT flux chart
 */
void XCopyDisk::diskFlux() {
    _esp->setTab("diskcopy");
    _esp->setMode("Disk Flux");
    _esp->setStatus("Drawing Disk Flux");
    _esp->setState(fluxDisk);
    _esp->resetDisk();

    _cancelOperation = false;

    if (!_floppy->diskChange()) {
        _graphics->drawText(0, 0, ST7735_RED, "No Disk Inserted");
        _esp->setStatus("No Disk Inserted");
        _audio->playBong(false);
        return;
    }

    String diskName = _floppy->getName();
    _esp->setDiskName(diskName);

    for (int trackNum = 0; trackNum < 160; trackNum++) {
        if (_cancelOperation) {
            OperationCancelled();
            return;
        }

        // read track
        _floppy->gotoLogicTrack(trackNum);
        int errors = readDiskTrack(trackNum, false, 1, true);
        // int errors = readTrack(true);

        if (errors != -1) {
            _floppy->analyseHist(true);
            drawFlux(trackNum);
        }
        else {
            _audio->playBong(false);
            _graphics->getTFT()->drawFastVLine(trackNum, 0, _graphics->getTFT()->height(), ST7735_MAGENTA);
        }
    }

    _audio->playBoing(false);

    _esp->setStatus("Disk Flux Complete");
}

/**
 * @brief Test floppy disk for read errors
 * 
 * @param retryCount number of retries when reading track
 */
void XCopyDisk::testDiskette(uint8_t retryCount) {
    _esp->setMode("Test Disk");
    _esp->setStatus("Testing Disk");  
    _esp->setState(testDisk);
    _esp->resetDisk();
    _esp->setTab("diskcopy");

    _cancelOperation = false;

    _graphics->drawDiskName("");
    _graphics->drawDisk();

    if (!_floppy->diskChange()) {
        _graphics->drawText(0, 10, ST7735_RED, "No Disk Inserted");
        Log << XCopyConsole::error("No Disk Inserted") << "\r\n";
        _esp->setStatus("No Disk Inserted");

        _audio->playBong(false);
        return;
    }

    String diskName = _floppy->getName();
    _graphics->drawDiskName(diskName);
    _graphics->getTFT()->drawFastHLine(0, 85, _graphics->getTFT()->width(), ST7735_GREEN);
    _esp->setDiskName(diskName);

    _trackMap.begin("TEST DISK", diskName);

    // MD5 setup
    MD5_CTX ctx;
    MD5::MD5Init(&ctx);

    for (int trackNum = 0; trackNum < 160; trackNum++) {
        if (_cancelOperation) {
            OperationCancelled(trackNum);
            return;
        }

        // read track
        readDiskTrack(trackNum, false, retryCount);

        // calculate MD5
        for (int sec = 0; sec < 11; sec++) {
            struct Sector *aSec = (Sector *)&_floppy->getTrack()[sec].sector;
            // calculate MD5
            MD5::MD5Update(&ctx, aSec->data, 512);
        }

        // draw flux
        _floppy->analyseHist(true);
        drawFlux(trackNum, 6, 85);
    }

    String sMD5 = ctxToMD5(&ctx);

    _trackMap.end("TEST COMPLETE - 160 tracks read");
    Log << "Floppy disk test MD5: " << sMD5 << "\r\n";

    _audio->playBoing(false);

    _esp->setStatus("Test Complete. <i class=\"fa-solid fa-hashtag\"></i> MD5: " + sMD5);
}

/**
 * @brief Scan floppy disk for full and empty tracks and update console and WebUI
 * 
 * @param retryCount number of retries when reading track
 */
void XCopyDisk::scanEmptyBlocks(uint8_t retryCount) {
    _esp->setMode("Scan Empty Blocks");
    _esp->setStatus("Scanning Disk");  
    _esp->setState(scanBlocks);
    _esp->resetDisk();
    _esp->setTab("diskmon");

    _cancelOperation = false;

    _graphics->drawDiskName("");
    _graphics->drawDisk();

    if (!_floppy->diskChange()) {
        _graphics->drawText(0, 10, ST7735_RED, "No Disk Inserted");
        Log << XCopyConsole::error("No Disk Inserted") << "\r\n";
        _esp->setStatus("No Disk Inserted");

        _audio->playBong(false);
        return;
    }

    String diskName = _floppy->getName();
    _graphics->drawDiskName(diskName);
    _graphics->getTFT()->drawFastHLine(0, 85, _graphics->getTFT()->width(), ST7735_GREEN);
    _esp->setDiskName(diskName);
    _esp->print("broadcast resetEmptyBlocks\r\n");

    Log << "\r\nScan blocks:\r\n";

    for (int trackNum = 0; trackNum < 160; trackNum++) {
        if (_cancelOperation) {
            OperationCancelled(trackNum);
            return;
        }

        // read track
        readDiskTrack(trackNum, false, retryCount);
        
        char track[3] = "";
        sprintf(track, "%02d", trackNum / 2);
        if (trackNum % 2 == 0) Log << "Track " + String(track) + " |";

        Log << " Side: " << trackNum % 2 << " | ";

        for (int sec = 0; sec < 11; sec++) {
            struct Sector *aSec = (Sector *)&_floppy->getTrack()[sec].sector;

            // MD5 setup
            MD5_CTX ctx;
            MD5::MD5Init(&ctx);
            MD5::MD5Update(&ctx, aSec->data, 512);
            String sMD5 = ctxToMD5(&ctx);
            
            bool empty = sMD5 == "BF619EAC0CDF3F68D496EA9344137E8B";
            Log << (empty ? XCopyConsole::background_green() + " " + String(sec) + " " + XCopyConsole::reset() : XCopyConsole::background_red() + " " + String(sec) + " " + XCopyConsole::reset());
            _esp->print("broadcast setEmptyBlock," + String(trackNum / 2) + "," + String(trackNum % 2) + "," + String(sec) + "," + (empty ? "true" : "false") + "\r\n");
            delay(5);
        }

        if (trackNum % 2) Log << "\r\n";

        // draw flux
        _floppy->analyseHist(true);
        drawFlux(trackNum, 6, 85, false);
    }

    _audio->playBoing(false);
}

// Block

/**
 * @brief Writes a series of non contiguous blocks to a binary file
 * 
 * @param blocks is a an array of 220 bytes. Each byte is equal to 8 sectors
 *               and each bit is set as 1 if you wish to write that block
 *               this allows non contiguous blocks to be written out to a bin file
 * @param offset offset into first block to start writing
 * @param size total size in bytes of file to be written
 * @param retryCount number of retries when reading disk
 * 
 * @result true if successful and false if failed when writing file
 * 
 * @todo TODO: write verify routine.
 */
bool XCopyDisk::writeBlocksToFile(byte blocks[], int offset, int size, String fileextension, uint8_t retryCount) {
    _cancelOperation = false;
    String statusText = "";
    String diskName = "";

    int totalReadErrors = 0;
    
    File ADFFile;

    // check if disk is present in floppy
    if (!_floppy->diskChange()) {
        Serial << "No disk inserted" << "\r\n";
        _audio->playBong(false);
        return false;
    }

    // get and set diskname
    diskName = _floppy->getName();
    Serial << "Diskname: " << diskName << "\r\n";

    // get filesnames
    String fullPath = generateADFFileName(diskName).replace(".adf", fileextension);
    Serial << "Filename: " << fullPath << "\r\n";

    // Open SD File
    XCopySDCard _sdcard;

    // card detect
    if (!_sdcard.cardDetect()) {
        Serial << "No SDCard detected" << "\r\n";
        _audio->playBong(false);
        return false;
    }

    // init
    if (!_sdcard.begin()) {
        Serial << "SD Init Failed" << "\r\n";
        _audio->playBong(false);
        return false;
    }

    // make ADF path
    if (!_sdcard.fileExists(SD_ADF_PATH)) _sdcard.makeDirectory(SD_ADF_PATH);

    // remove sdcard adf & log files if they exist
    if (_sdcard.fileExists(fullPath)) _sdcard.deleteFile(fullPath.c_str());

    // open sdcard files
    SdFile::dateTimeCallback(dateTime);
    ADFFile = _sdcard.getSdFat().open(fullPath.c_str(), FILE_WRITE);
    SdFile::dateTimeCallbackCancel();

    // if adf file failed top open
    if (!ADFFile) {
        ADFFile.close();
        Serial << "File '" + fullPath + "' failed to open on the SD card" << "\r\n";
        _audio->playBong(false);
        return false;
    }

    DiskLocation dl;
    int currentTrack = -1;
    int filesize = 0;
    int lastblock = 0;    
    for (size_t index = 0; index < 220; index++) {
        for (size_t bit = 0; bit < 8; bit++) {
            int mask = 1 << bit;
            if ((blocks[index] & mask) > 0) {
                lastblock = (index * 8) + bit;
            }
        }
    }

    for(size_t index = 0; index < 220; index++) {
        for (size_t bit = 0; bit < 8; bit++) {
            int mask = 1 << bit;

            // if write block
            if ((blocks[index] & mask) > 0) {
                int block = (index * 8) + bit;
                dl.setBlock(block);

                if (dl.logicalTrack() != currentTrack) {
                    int readResult = readDiskTrack(dl.logicalTrack(), false, retryCount, true);
                    if (readResult != 0) {
                        // if there has been error on either side, set error for whole cylinder else increment retry count
                        Serial << "Read Errors: " << ++totalReadErrors << "\r\n";
                    }
                }

                const struct Sector *aSec = (Sector *)&_floppy->getTrack()[dl.sector()].sector;
                // set offset for first and last sectors
                int sectorsize = filesize == 0 ? 512 - offset : 512;
                int sectoroffset = filesize == 0 ? offset : 0;
                if (dl.block() == lastblock)  { 
                    sectorsize = size - filesize;
                }
                // modrip 385 50 61710
                
                int byteswritten = ADFFile.write(aSec->data + sectoroffset, sectorsize);
                if (byteswritten <= 0) { 
                    Log << "Write error.";
                    return false;
                }
                filesize += byteswritten;
                currentTrack = dl.logicalTrack();

                // Serial << block << " | logtrack: " << dl.logicalTrack << " | track: " << dl.track << " | side: " << dl.side << " | sector: " << dl.sector << "\r\n";
            }
        }
    }

    Log << "File Size: " + String(filesize) + "\r\n";

    ADFFile.close();
    _audio->playBoing(false);

    return true;
}

/**
 * @brief Writes a binary file to the floppy disk
 * 
 * @param BinFileName path to binary file on SDCard that will be written to disk
 * @param startBlock the starting block for the binary file
 * @param retryCount number of retries when reading track
 * 
 * @result true if successful and false if failed when writing file
 * 
 * @todo TODO: write verify routine. Support offset
 */
bool XCopyDisk::writeFileToBlocks(String BinFileName, int startBlock, uint8_t retryCount) {
    if (!_floppy->diskChange()) {
        Log << "No Disk Inserted\r\n";
        _audio->playBong(false);
        return false;
    }

    if (_floppy->getWriteProtect()) {
        _graphics->drawText(0, 10, ST7735_RED, "Disk Write Protected");
        Log << XCopyConsole::error("Disk Write Protected") << "\r\n";
        _audio->playBong(false);
        return false;
    }

    if (startBlock < 0 || startBlock > 1759) {
        Log << "Invalid block number: " + String(startBlock) + "\r\n";
        _audio->playBong(false);
        return false;
    }

    XCopySDCard _sdcard;

    if (!_sdcard.begin()) {
        Log << "SD Init Failed\r\n";
        _audio->playBong(false);
        return false;
    }

    if (!_sdcard.fileExists(BinFileName)) {
        Log << "File: '" + BinFileName + "' does not exist.\r\n";
        _audio->playBong(false);
        return false;
    }

    File BinFile;
    BinFile = _sdcard.getSdFat().open(BinFileName.c_str(), FILE_READ);

    if (!BinFile) {
        Log << "SD File Open Failed\r\n";
        _audio->playBong(false);
        BinFile.close();
        return false;
    }

    _esp->setMode("Write File to Disk");
    _esp->setStatus("Writing File");  
    _esp->resetDisk();
    _esp->setTab("diskcopy");
    _graphics->clearScreen();
    _graphics->drawDisk();
    _graphics->drawText(0, 0, ST7735_WHITE, "Write File", true);
    _graphics->getTFT()->drawFastHLine(0, 85, _graphics->getTFT()->width(), ST7735_GREEN);

    _floppy->setAutoDensity(false);
    _floppy->setMode(DD); // DD
    delay(5);
    _floppy->setCurrentTrack(-1);

    _floppy->motorOn();
    _floppy->seek0();
    delay(100);

    DiskLocation startdl;
    startdl.setBlock(startBlock);   
    int blockCount = ceil(BinFile.size() / 512.0f);
    DiskLocation enddl;
    enddl.setBlock(startBlock + blockCount);

    Log << "File Size: " + String(BinFile.size()) + "\r\nWriting " + String(blockCount) + " blocks\r\n";
    Log << "----------------------------------------------------------\r\n";
    Log << "Start | Block: " + String(startdl.block()) + " Track: " + String(startdl.track()) + " Side: " + String(startdl.side()) + " Sector: " + String(startdl.sector()) + "\r\n";
    Log << "  End | Block: " + String(enddl.block()) + " Track: " + String(enddl.track()) + " Side: " + String(enddl.side()) + " Sector: " + String(enddl.sector()) + "\r\n";
    Log << "----------------------------------------------------------\r\n";

    for (int logicalTrack = startdl.logicalTrack(); logicalTrack <= enddl.logicalTrack(); logicalTrack++) {
        int startSector = logicalTrack == startdl.logicalTrack() ? startdl.sector() : 0;
        int endSector = logicalTrack == enddl.logicalTrack() ? enddl.sector() : 11;

        // if writing a partial track, read existing track into track buffer
        if (startSector != 0 || endSector || 11) {
            int readResult = readDiskTrack(logicalTrack, false, retryCount);

            // read error
            if (readResult != 0) {
                Log << "Read error reading existing track for partial write. Aborted.\r\n";
                return false;
            }
        }

        // console output
        DiskLocation tempdl;
        tempdl.setBlock(logicalTrack, startSector);
        Log << "Write | Track: " + String(tempdl.track()) + " Side: " + String(tempdl.side()) + " Sectors: ";

        // replace blocks in track buffer with blocks from binary file
        for (int i = startSector; i < endSector; i++) {
            Log << String(i) + (i != endSector - 1 ? "," : "" );
            byte buffer[512];
            memset(buffer, 0, 512);
            int read = BinFile.read(buffer, sizeof(buffer));
            if (read == 0) {
                Log << "Error: 0 Bytes read\r\n";
            }
            struct Sector *aSec = (Sector *)&_floppy->getTrack()[i].sector[0];
            memcpy(aSec->data, buffer, 512);
        }
        Log << "\r\n";

        // encode track
        _floppy->floppyTrackMfmEncode(logicalTrack, (byte *)_floppy->getTrack(), _floppy->getStream());

        // write track
        int result = writeDiskTrack(logicalTrack, retryCount);
        // read error
        if (result == -1) {
            Log << "Error writing track. Aborted.\r\n";
            return false;
        }
        if (result > 0) {
            Log << "Writing track required " + String(result) + " retries.\r\n";
            return false;
        }

        delay(100);
    }

    BinFile.close();
    _audio->playBoing(false);

    return true;
}

// Search - ASCII & Tracker Module

/**
 * @brief process ASCII search result. Used as function pointer in search
 * 
 * @param obj pointer to XCopyDisk object used in static function
 * @param text ASCII search text
 * @param dl location on disk of search result
 * @param offset offset into block for search result
 * @param retryCount number of retries when reading track
 * 
 * @result return search result block, offset and size in blocks
 */
SearchResult XCopyDisk::processAscii(XCopyDisk* obj, String text, DiskLocation dl, int offset, uint8_t retryCount) {
    Log << "Found: '" + text + "' | Block: " + String(dl.block()) + " Logical Track: " + String(dl.logicalTrack()) +  " Track: " + String(dl.track()) + " Side: " + String(dl.side()) + " Sector: " + String(dl.sector()) + " Offset: 0x";
    char f_offset[5];
    sprintf(f_offset, "%04x", offset);
    Log << String(f_offset) + "\r\n";
    Log << "\r\n";
    // static, so the drive comes in on the instance the search is running against
    obj->_floppy->printAmigaSector(dl.sector());
    SearchResult sr;
    sr.block = dl.block();
    sr.offset = offset;
    sr.size = 0;
    return sr;
}

/**
 * @brief process tracker module search result. Used as function pointer in search
 * 
 * @param obj pointer to XCopyDisk object used in static function
 * @param text Module magic bytes search text i.e M.K, M!K!, 8CHN etc
 * @param dl location on disk of search result
 * @param offset offset into block for search result
 * @param retryCount number of retries when reading track
 * 
 * @result return search result block, offset and size in blocks
 */
SearchResult XCopyDisk::processModule(XCopyDisk* obj, String text, DiskLocation dl, int offset, uint8_t retryCount) {
    // the MOD file is found by searching for some magic bytes such as M.K
    // these bytes are at an offset of 1080 bytes in the header.
    // this means the module actually starts a few blocks before the block
    // the magic bytes were found on.
    // https://www.eblong.com/zarf/blorb/mod-spec.txt

    int remainingBytes = 1080 - offset;                                  // remaining bytes of header on other blocks / bytes before 0th bytes of track containing M.K.
    int modStartBlock = dl.block() - ceil(remainingBytes / 512.0f);        // block that MOD starts on
    int modStartBlockOffset = 512 - (remainingBytes % 512);              // byte offset of block that MOD starts on

    // display disk location of module

    dl.setBlock(modStartBlock);
    Log << "Possible Mod Location: | Block: " + String(dl.block()) + " Logical Track: " + String(dl.logicalTrack()) +  " Track: " + String(dl.track()) + " Side: " + String(dl.side()) + " Sector: " + String(dl.sector()) + " Offset: 0x";
    char f_offset[5];
    sprintf(f_offset, "%04x", modStartBlockOffset);
    Log << String(f_offset) + "\r\n";

    // load mod header from disk into modinfo header

    ModInfo modinfo;
    obj->loadModuleHeader(dl, modStartBlockOffset, &modinfo, retryCount);

    // process and print module info

    modinfo.Process();
    modinfo.Print();

    Log << "Example Command for this module: modrip " + String(dl.block()) + " " + String(modStartBlockOffset) + " " + String(modinfo.filesize) + "\r\n\r\n";

    SearchResult sr;
    sr.block = modStartBlock;
    sr.offset = modStartBlockOffset;
    sr.size = modinfo.filesize;
    return sr;
}

/**
 * @brief search memory for specificed string
 * 
 * @param searchText string to search memory for
 * @param memory pointer to memory to search
 * @param memorySize total amount of bytes of to search
 * 
 * @result index into memory for search result, -1 if not found.
 */
int XCopyDisk::searchMemory(String searchText, byte* memory, size_t memorySize) { 
    size_t sSize = searchText.length();
    size_t sIndex = 0;
    searchText = searchText.toLowerCase();

    for(size_t mIndex = 0; mIndex < memorySize; mIndex++) {
        byte m1 = memory[mIndex];
        byte m2 = (m1 >= 65 && m1 <= 90) ? m1 + 32 : m1;

        if (m1 == searchText[sIndex] || m2 == searchText[sIndex]) {
            if (++sIndex == sSize) return (mIndex - sSize) + 1;
        } 
        else { sIndex = 0; }
    }

    return -1;
}

/**
 * @brief Search and process content on floppy disk
 * 
 * @param text text to search floppy for
 * @param retryCount number of retries when reading track
 * @param processor the function used to process successful searches
 * 
 * @result returns true if the search process was successful
 */
bool XCopyDisk::search(String text, uint8_t retryCount, SearchProcessor processor) {
    _cancelOperation = false;

    // check if disk is present in floppy
    if (!_floppy->diskChange()) {
        Serial << "No disk inserted" << "\r\n";
        _audio->playBong(false);
        return false;
    }

    _esp->resetDisk();
    _esp->setTab("diskmon");
    _esp->clearHighlightedBlocks();
    _graphics->drawDisk();
    _graphics->drawText(0, 0, ST7735_WHITE, "ASCII Search", true);
    _graphics->getTFT()->drawFastHLine(0, 85, _graphics->getTFT()->width(), ST7735_GREEN);

    Serial << "\r\nSearch blocks:\r\nSearching ...\r\n";

    for (int trackNum = 0; trackNum < 160; trackNum++) {
        if (_cancelOperation) {
            OperationCancelled(trackNum);
            Log << "Canceled.\r\n";
            return false;
        }

        // read track
        readDiskTrack(trackNum, false, retryCount);
        
        char track[3] = "";
        sprintf(track, "%02d", trackNum / 2);

        for (int sec = 0; sec < 11; sec++) {
            struct Sector *aSec = (Sector *)&_floppy->getTrack()[sec].sector;

            if (text == "\033MOD") {
                for (int i=0; i<10; i++) {
                    switch(i) {
                        case 0:
                            text = "M.K.";
                            break;
                        case 1:
                            text = "M!K!";
                            break;
                        case 2:
                            text = "FLT4";
                            break;
                        case 3:
                            text = "FLT8";
                            break;
                        case 4:
                            text = "2CHN";
                            break;
                        case 5:
                            text = "5CHN";
                            break;
                        case 6:
                            text = "6CHN";
                            break;
                        case 7:
                            text = "7CHN";
                            break;
                        case 8:
                            text = "8CHN";
                            break;
                        case 9:
                            text = "OCTA";
                            break;
                        default:
                            text = "ERROR!";
                            break;
                    }
                    int offset = searchMemory(text, aSec->data, 512);           
                    if (offset != -1) {
                        DiskLocation dl;
                        dl.setBlock(trackNum, sec);
                        SearchResult sr = processor(this, text, dl, offset, retryCount);                
                        dl.setBlock(sr.block);
                        _esp->highlightBlock(dl.track(), dl.side(), dl.sector(), sr.size == 0 ? 1 : ceil(sr.size / 512.0f), true);
                        Serial << "Searching ...\r\n";
                    };
                }
                text = "\033MOD";
            } else {
                int offset = searchMemory(text, aSec->data, 512);           
                if (offset != -1) {
                    DiskLocation dl;
                    dl.setBlock(trackNum, sec);
                    SearchResult sr = processor(this, text, dl, offset, retryCount);                
                    dl.setBlock(sr.block);
                    _esp->highlightBlock(dl.track(), dl.side(), dl.sector(), sr.size == 0 ? 1 : ceil(sr.size / 512.0f), true);
                    Serial << "Searching ...\r\n";
                };
            }
        }

        // draw flux
        _floppy->analyseHist(true);
        drawFlux(trackNum, 6, 85, false);
    }

    Serial << "Done.\r\n";
    _audio->playBoing(false);
    return true;
}

/**
 * @brief load module header from disk into modinfo class
 * 
 * @param dl location on floppy disk of module
 * @param offset offset into block for module start
 * @param modinfo modinfo class used to store module details
 * @param retryCount number of retries when reading track
 */
void XCopyDisk::loadModuleHeader(DiskLocation dl, int offset, ModInfo* modinfo, uint8_t retryCount) {
    readDiskTrack(dl.logicalTrack(), false, retryCount);
    struct Sector *aSec = (Sector *)&_floppy->getTrack()[dl.sector()].sector;    
    memcpy(&modinfo->header[0], &aSec->data[offset], 512 - offset);
    size_t size = 512 - offset;

    int currentTrack = dl.logicalTrack();
    dl.setBlock(dl.block() + 1);
    if (dl.logicalTrack() != currentTrack) {
        readDiskTrack(dl.logicalTrack(), false, retryCount);
    }
    aSec = (Sector *)&_floppy->getTrack()[dl.sector()].sector;
    memcpy(&modinfo->header[size], &aSec->data[0], 512);

    size += 512;
    currentTrack = dl.logicalTrack();

    if (size < 1084) {
        currentTrack = dl.logicalTrack();
        dl.setBlock(dl.block() + 1);
        if (dl.logicalTrack() != currentTrack) {
            readDiskTrack(dl.logicalTrack(), false, retryCount);
        } 
        aSec = (Sector *)&_floppy->getTrack()[dl.sector()].sector;
        memcpy(&modinfo->header[size], &aSec->data[0], 1084 - size);
    }
}

/**
 * @brief Save mod from floppy drive to SDCard
 * 
 * @param dl location on floppy disk of module
 * @param offset offset into block for module start
 * @param size size of module file in bytes
 * @param retryCount number of retries when writing track
 * 
 * @result returns true if the search process was successful
 */
bool XCopyDisk::modRip(DiskLocation dl, int offset, int size, uint8_t retryCount) {
    int startBlock = dl.block();
    int endblock = (dl.block() + ceil((size + offset) / 512.0f)) - 1;
    byte blocks[220];
    int blockindex = 0;
    byte packedblocks = 0;

    // loop through all blocks and build packed block array
    for(uint16_t index = 0; index < 1760; index++) {
        if (index >= startBlock && index <= endblock) {
            packedblocks |= 1 << (index % 8);
        }

        if ((index + 1) % 8 == 0) {
            blocks[blockindex++] = packedblocks;
            packedblocks = 0;
        }
    }

    return writeBlocksToFile(blocks, offset, size, ".mod", retryCount);
}

// MD5

/**
 * @brief Construct MD5 string of ctx struct from MD5.h library
 * 
 * @param ctx ctx struct defined in MD5.h used to store MD5 hash details
 * 
 * @result MD5 string
 */
String XCopyDisk::ctxToMD5(MD5_CTX *ctx) {
    String sMD5 = "";
    unsigned char result[20];
    MD5::MD5Final(result, ctx);
    char bMD5[3];
    for (size_t i = 0; i < 16; i++) {
        sprintf(bMD5, "%02X", result[i]);
        sMD5.append(String(bMD5));
    }
    return sMD5;
}

/**
 * @brief Calculate MD5 hash of ADF file on SDCard 
 * 
 * @param ADFFileName path to ADF file on SDCard
 * @param retryCount number of retries when reading track
 * 
 * @result MD5 string
 */
String XCopyDisk::adfToMD5(String ADFFileName) {
        FatFile file;
        bool fresult = file.open(ADFFileName.c_str());
        if (!fresult) {
            Serial << F("unable to open: '") + ADFFileName + F("'\r\n");
            return "";
        }

        const size_t bufferSize = 2048;
        char *buffer = (char *)XCopyScratch::borrow("disk.adfToMD5", bufferSize);
        if (buffer == nullptr) {
            file.close();
            return "";
        }

        MD5_CTX ctx;
        MD5::MD5Init(&ctx);

        // read() returns -1 on error, and readsize was a size_t: a failed read became
        // MD5Update(..., SIZE_MAX) and a loop that never ended, because the (size_t)-1
        // also tested > 0. Same shape as the bug already fixed in
        // XCopyTransfer::sendFile().
        int readsize = 0;
        while ((readsize = file.read(buffer, bufferSize)) > 0) {
            MD5::MD5Update(&ctx, buffer, readsize);
        }

        XCopyScratch::release((const uint8_t *)buffer);
        file.close();

        if (readsize < 0) return "";

        return ctxToMD5(&ctx);
}

/**
 * @brief Calculate MD5 hash of tempory ADF in Flash memory
 * 
 * @result MD5 string
 */
String XCopyDisk::flashToMD5() {
    SerialFlashFile ADFFlashFile;

   if (!SerialFlash.begin(PIN_FLASHCS)) {
        _graphics->drawText(0, 10, ST7735_RED, "Serial Flash Init Failed");
        Log << XCopyConsole::error("Serial Flash Init Failed") << "\r\n";
        _esp->setStatus("Serial Flash Init Failed");
        _audio->playBong(false);
        return "";
    }

    ADFFlashFile = SerialFlash.open("DISKCOPY.TMP");
    if (!ADFFlashFile) {
        _graphics->drawText(0, 10, ST7735_RED, "Serial Flash File Open Failed");
        Log << XCopyConsole::error("Serial Flash File Open Failed") << "\r\n";
        _esp->setStatus("Serial Flash File Open Failed");
        _audio->playBong(false);
        ADFFlashFile.close();
        return "";
    }

    ADFFlashFile.seek(0);

    // MD5 setup
    MD5_CTX ctx;
    MD5::MD5Init(&ctx);

    // write ADF file
    for (int trackNum = 0; trackNum < 160; trackNum++) {
        // read track from ADF file into track buffer
        for (int i = 0; i < 11; i++) {
            byte buffer[512];
            ADFFlashFile.read(buffer, sizeof(buffer));
            // calculate MD5
            MD5::MD5Update(&ctx, buffer, 512);

        }
    }

    return ctxToMD5(&ctx);
}
