AdamKeher/XCopyStandalone/src/XCopy/XCopyGraphics.cpp

#include "XCopyGraphics.h"

void XCopyGraphics::begin(TFT_ST7735 *tft)
{
    _tft = tft;
}

void XCopyGraphics::drawHeader()
{
    bmpDraw("XCPYLOGO.BMP", 0, 0);
}

void XCopyGraphics::drawTrack(uint8_t track, uint8_t side, bool drawText, bool retry, int retryCount, bool verify, uint16_t color)
{
    // 5px blocks, not 6. Ten columns would fit at 6px across - two sides of them plus
    // the gap is 155 of the panel's 160 - but GRID_ROWS is 9 now, and 25 + 9 * 7 puts
    // the bottom row at 88. diskToADF() clears from y 85 down for the status text, so
    // the last row of a copy would be wiped as it was drawn. At 5px it ends at 79.
    const uint8_t blockSize = 5;
    if (drawText)
    {
        this->drawText(0, 10, ST7735_WHITE, "TRACK: ", true);
        this->drawText(ST7735_YELLOW, String(track));
        this->drawText(67, 10, WHITE, "SIDE: ");
        this->drawText(ST7735_YELLOW, String(side));

        if (retry)
        {
            this->drawText(115, 10, ST7735_RED, "RETRY " + String(retryCount));
        }

        if (verify)
        {
            this->drawText(115, 10, ST7735_GREEN, "VERIFY");
        }
    }

    const int yoffset = 25;
    const int xoffset = 5;
    const int sidegap = 10;
    const int tracksperline = GRID_COLS;
    const int col = track / tracksperline;
    const int row = track - (col * tracksperline);

    int x = (row * (blockSize + 1)) + xoffset + (side == 1 ? ((blockSize + 1) * tracksperline) + sidegap : 0);
    int y = (col * (blockSize + 1)) + yoffset;

    _tft->fillRect(x, y, blockSize, blockSize, color);
}

void XCopyGraphics::drawDiskName(String name)
{
    drawText(0, 0, ST7735_WHITE, "DISKNAME: ", true);
    drawText(ST7735_YELLOW, name);
}

void XCopyGraphics::drawDisk(uint8_t start, uint16_t color)
{
    for (int x = start; x < MAX_TRACKS; x++)
    {
        if (x % 2 == 0)
            drawTrack(x / 2, 0, false, false, 0, false, color);
        else
            drawTrack(x / 2, 1, false, false, 0, false, color);
    }
}

void XCopyGraphics::drawText(uint8_t x, uint8_t y, uint16_t color, String text, bool clearLine)
{
    if (clearLine)
        _tft->fillRect(0, y, _tft->width(), 10, ST7735_BLACK);

    _tft->setCursor(x, y);
    _tft->setTextColor(color);
    _tft->print(text);
}

void XCopyGraphics::drawText(uint16_t color, String text)
{
    _tft->setTextColor(color);
    _tft->print(text);
}

void XCopyGraphics::drawText(String text)
{
    _tft->print(text);
}

uint16_t XCopyGraphics::LerpRGB(uint16_t a, uint16_t b, float t)
{
    uint8_t ar = 0;
    uint8_t ag = 0;
    uint8_t ab = 0;
    uint8_t br = 0;
    uint8_t bg = 0;
    uint8_t bb = 0;

    _tft->Color565ToRGB(a, ar, ag, ab);
    _tft->Color565ToRGB(b, br, bg, bb);

    uint8_t cr = ar + (br - ar) * t;
    uint8_t cg = ag + (bg - ag) * t;
    uint8_t cb = ab + (bb - ab) * t;

    return _tft->Color565(cr, cg, cb);
}

void XCopyGraphics::bmpDraw(const char *filename, uint16_t x, uint16_t y)
{
    SerialFlashFile flashFile;
    int bmpWidth, bmpHeight;            // W+H in pixels
    uint8_t bmpDepth;                   // Bit depth (currently must be 24)
    uint32_t bmpImageoffset;            // Start of image data in file
    uint32_t rowSize;                   // Not always = bmpWidth; may have padding
    uint8_t sdbuffer[3 * BUFFPIXEL];    // pixel buffer (R+G+B per pixel)
    uint8_t buffidx = sizeof(sdbuffer); // Current position in sdbuffer
    boolean goodBmp = false;            // Set to true on valid header parse
    boolean flip = true;                // BMP is stored bottom-to-top
    int w, h, row, col;
    uint8_t r, g, b;
    uint32_t pos = 0;

    if ((x >= _tft->width()) || (y >= _tft->height()))
        return;

    flashFile = SerialFlash.open(filename);
    if (!flashFile) {
        Serial.print(F("File not found"));
        return;
    }

    // Parse BMP header
    if (read16(flashFile) == 0x4D42)
    { // BMP signature

        (void)read32(flashFile); // read & ignore filesize

        (void)read32(flashFile); // Read & ignore creator bytes

        bmpImageoffset = read32(flashFile); // Start of image data

        // Read DIB header
        (void)read32(flashFile); // read & ignore headerSize

        bmpWidth = read32(flashFile);
        bmpHeight = read32(flashFile);
        if (read16(flashFile) == 1)
        {                                 // # planes -- must be '1'
            bmpDepth = read16(flashFile); // bits per pixel
            if ((bmpDepth == 24) && (read32(flashFile) == 0))
            { // 0 = uncompressed

                goodBmp = true; // Supported BMP format -- proceed!

                // BMP rows are padded (if needed) to 4-byte boundary
                rowSize = (bmpWidth * 3 + 3) & ~3;

                // If bmpHeight is negative, image is in top-down order.
                // This is not canon but has been observed in the wild.
                if (bmpHeight < 0)
                {
                    bmpHeight = -bmpHeight;
                    flip = false;
                }

                // Crop area to be loaded
                w = bmpWidth;
                h = bmpHeight;
                if ((x + w - 1) >= _tft->width())
                    w = _tft->width() - x;
                if ((y + h - 1) >= _tft->height())
                    h = _tft->height() - y;

                for (row = 0; row < h; row++)
                { // For each scanline...

                    // Seek to start of scan line.  It might seem labor-
                    // intensive to be doing this on every line, but this
                    // method covers a lot of gritty details like cropping
                    // and scanline padding.  Also, the seek only takes
                    // place if the file position actually needs to change
                    // (avoids a lot of cluster math in SD library).
                    if (flip) // Bitmap is stored bottom-to-top order (normal BMP)
                        pos = bmpImageoffset + (bmpHeight - 1 - row) * rowSize;
                    else // Bitmap is stored top-to-bottom
                        pos = bmpImageoffset + row * rowSize;
                    if (flashFile.position() != pos)
                    { // Need seek?
                        flashFile.seek(pos);
                        buffidx = sizeof(sdbuffer); // Force buffer reload
                    }

                    for (col = 0; col < w; col++)
                    { // For each pixel...
                        // Time to read more pixel data?
                        if (buffidx >= sizeof(sdbuffer))
                        { // Indeed
                            flashFile.read(sdbuffer, sizeof(sdbuffer));
                            buffidx = 0; // Set index to beginning
                        }

                        // Convert pixel from BMP to TFT format, push to display
                        b = sdbuffer[buffidx++];
                        g = sdbuffer[buffidx++];
                        r = sdbuffer[buffidx++];

                        // _tft->push(_tft->Color565(r, g, b));

                        // alternative tries
                        _tft->drawPixel(x + col, y + row, _tft->Color565(r, g, b));

                    } // end pixel
                } // end scanline
            } // end goodBmp
        }
    }

    flashFile.close();

    offset = 0;

    if (!goodBmp)
        Serial.println(F("BMP format not recognized."));
}

void XCopyGraphics::rawDraw(const char *filename, uint16_t x, uint16_t y)
{
    SerialFlashFile bmpFile;
    int bmpWidth, bmpHeight; // W+H in pixels
    uint8_t bmpDepth;        // Bit depth (currently must be 24)
    boolean goodBmp = false; // Set to true on valid header parse
    uint16_t w, h;

    if ((x >= _tft->width()) || (y >= _tft->height()))
        return;

    // Open requested file on SD card
    bmpFile = SerialFlash.open(filename);
    if (!bmpFile) {
        Serial.print(F("File not found\r\n"));
        return;
    }

    /*
       Parse BMP header.

       Every read here has to happen even where the value is thrown away: read16()
       and read32() walk a shared file offset, so a field that is not read is not
       skipped either - it is simply handed to whatever is read next. Dropping the
       DIB header size is what broke this. It went with the unused local that held
       it, which moved the width into it, the height into the width and the low
       half of the height into the plane count; 128 is not 1, so the parse bailed
       and every flash thumbnail reported "565 format not recognized".
    */
    if (read16(bmpFile) == 0x4D42)
    { // BMP signature
        read32(bmpFile);       // fileSize
        (void)read32(bmpFile); // Read & ignore creator bytes
        uint32_t bmpImageoffset = read32(bmpFile);
        (void)read32(bmpFile); // DIB header size - read to skip it, see above
        bmpWidth = read32(bmpFile);
        bmpHeight = read32(bmpFile);
        if (read16(bmpFile) == 1)
        {                               // # planes -- must be '1'
            bmpDepth = read16(bmpFile); // bits per pixel
            if (read32(bmpFile) == 0) // 0 = uncompressed
            {
                if (bmpHeight < 0)
                {
                    bmpHeight = -bmpHeight;
                }

                // Crop area to be loaded
                w = bmpWidth;
                h = bmpHeight;
                if ((x + w - 1) >= _tft->width())
                    w = _tft->width() - x;
                if ((y + h - 1) >= _tft->height())
                    h = _tft->height() - y;

                // Set TFT address window to clipped image bounds
                _tft->startPushData(x, y, x + w - 1, y + h - 1);

                if (bmpDepth == 16) //565 format
                {
                    goodBmp = true; // Supported BMP format -- proceed!

                    uint16_t buffer[BUFFPIXELCOUNT]; // pixel buffer

                    // The offset the header gave, rather than the 54 a 40 byte DIB
                    // header happens to put it at.
                    bmpFile.seek(bmpImageoffset);
                    uint32_t totalPixels = (uint32_t)bmpWidth * (uint32_t)bmpHeight;
                    uint16_t numFullBufferRuns = totalPixels / BUFFPIXELCOUNT;

                    for (uint32_t p = 0; p < numFullBufferRuns; p++)
                    {                        
                        // read pixels into the buffer
                        bmpFile.read(buffer, 2 * BUFFPIXELCOUNT);
                        // push them to the diplay
                        for (int i = 0; i < BUFFPIXELCOUNT; i++)
                        {
                            _tft->pushColor(buffer[i]);
                        }
                    }

                    // Render any remaining pixels that did not fill the buffer. The
                    // loop runs to remainingPixels, not to BUFFPIXELCOUNT: only that
                    // many were read, and the rest of the buffer is the previous run
                    // still sitting in it. An image whose pixel count is a multiple
                    // of BUFFPIXELCOUNT never gets here, which is why every built in
                    // thumbnail - 160 x 128, twenty full runs - hid it.
                    uint32_t remainingPixels = totalPixels % BUFFPIXELCOUNT;
                    if (remainingPixels > 0)
                    {
                        bmpFile.read(buffer, 2 * remainingPixels);
                        for (uint32_t i = 0; i < remainingPixels; i++)
                        {
                            _tft->pushColor(buffer[i]);
                        }
                    }
                }
                else
                {
                    Serial << "Unsupported Bit Depth.\r\n";
                }

                _tft->endPushData();
            }
        }
    }

    offset = 0;

    bmpFile.close();
    
    if (!goodBmp)
        Serial.print("565 format not recognized.\r\n");
}

// These read 16- and 32-bit types from the SD card file.
// BMP data is stored little-endian, Arduino is little-endian too.
// May need to reverse subscript order if porting elsewhere.

uint16_t XCopyGraphics::read16(SerialFlashFile f)
{
    uint16_t result;

    char buffer[2];
    f.seek(offset);
    f.read(buffer, 2);
    offset = offset + 2;

    ((uint8_t *)&result)[0] = (uint16_t)buffer[0]; // LSB
    ((uint8_t *)&result)[1] = (uint16_t)buffer[1]; // MSB
    return result;
}

uint32_t XCopyGraphics::read32(SerialFlashFile f)
{
    uint32_t result;

    char buffer[4];
    f.seek(offset);
    f.read(buffer, 4);
    offset = offset + 4;

    ((uint8_t *)&result)[0] = (uint16_t)buffer[0]; // LSB
    ((uint8_t *)&result)[1] = (uint16_t)buffer[1];
    ((uint8_t *)&result)[2] = (uint16_t)buffer[2];
    ((uint8_t *)&result)[3] = (uint16_t)buffer[3]; // MSB
    return result;
}
