AdamKeher/XCopyStandalone/src/XCopy/XCopyCommand.cpp

#include "XCopyCommand.h"
#include "XCopyFixed.h"
#include "XCopyScratch.h"
#include <Streaming.h>
#include <SerialFlash.h>

/*
   The console.

   Everything the interpreter knows about the commands themselves lives in
   XCopyCommandTable.cpp. This file is the plumbing around it: read a line, find
   the command, let XCopyArgs check the arguments against the table, and call the
   one handler. What it is not any more is a 45 arm chain of string compares with
   the argument parsing, the disk and card checks, and a second hand written copy
   of the help all folded into it.
*/

// Frame geometry for the help table. The same 88 column box XCopyTrackMap and the
// head calibration panel are drawn in, so the console looks like one program.
static const uint8_t HELP_LEFT = 31;
static const uint8_t HELP_RIGHT = 52;
static const uint8_t HELP_INNER = 86;

static String pad(const String &text, uint8_t width)
{
    String out = text;
    // Truncate rather than let a long entry push the right hand edge out. Nothing
    // in the table is close, but a row that breaks the frame is how a table stops
    // being readable at all.
    if (out.length() > width)
        out.remove(width);
    while (out.length() < width)
        out += ' ';

    return out;
}

static void helpRow(const String &left, const String &right)
{
    Log << "| " + pad(left, HELP_LEFT) + "| " + pad(right, HELP_RIGHT) + "|\r\n";
}

static void helpWide(const String &text)
{
    Log << "| " + pad(text, HELP_INNER - 1) + "|\r\n";
}

static void helpRule(char left, char fill, char joint, char right)
{
    String line;
    line.reserve(90);
    line += left;
    for (uint8_t i = 0; i < HELP_LEFT + 1; i++)
        line += fill;
    line += joint;
    for (uint8_t i = 0; i < HELP_RIGHT + 1; i++)
        line += fill;
    line += right;
    line += "\r\n";
    Log << line;
}

/*
   The two things the editor and the completer are handed instead of reaching for
   them, so that neither has to include the log or the SD card. See XCopyConsoleIO.h.
*/
static void writeConsole(const String &text)
{
    Log << text;
}

/*
   What Tab offers for a path, which is either the card or a mounted image.

   The completer never learns there are two: it asks for the contents of a
   directory and gets them, exactly as before. Routing on the device prefix here
   is what keeps XCopyComplete depending on nothing but String, and therefore
   keeps it in the host test suite - which is the same reason XCopyConsoleIO.h
   made this a function pointer in the first place.
*/
struct VolumeListing
{
    XCopyDirVisit visit;
    void *context;
};

static void offerVolumeEntry(void *context, const struct AdfEntry *entry)
{
    const VolumeListing *listing = (const VolumeListing *)context;

    if (entry->name == NULL)
        return;

    // Bare names. The completer puts the device and the directory back on itself,
    // from the part of the token it split off before asking - the same contract
    // the SD listing above has always had.
    listing->visit(listing->context, String(entry->name),
                   entry->type == ADF_ST_DIR);
}

static void listDirectory(const String &directory, XCopyDirVisit visit, void *context)
{
    XCopyPath path;
    if (xcopySplitPath(directory, path) && path.qualified && !path.isCard())
    {
        XCopyAdfMount::Slot *slot = XCopyAdfMount::find(path.device);
        if (slot == nullptr || !slot->mounted())
            return;

        String leaf;
        // Quietly: a Tab on a path that does not exist yet is a question, not a
        // mistake, and printing an error into the middle of a line being typed
        // would be worse than offering nothing.
        XCopyAdf::setEcho(false);
        const bool reached = XCopyAdfMount::walkTo(*slot, path.rest, leaf);
        XCopyAdf::setEcho(true);
        if (!reached)
            return;

        struct AdfEntryBlock scratch[2];
        VolumeListing listing = {visit, context};
        adfWalkDir(slot->vol, slot->vol->curDirPtr, scratch,
                   offerVolumeEntry, nullptr, &listing);
        return;
    }

    XCopySDCard sdcard;

    if (!sdcard.cardDetect() || !sdcard.begin() || !sdcard.open(directory))
        return;

    while (sdcard.next())
    {
        const XCopyFile &file = sdcard.getfile();
        visit(context, file.filename, file.isDirectory);
    }
}

XCopyCommandLine::XCopyCommandLine(String version, XCopyESP8266 *esp, XCopyConfig *config, XCopyDisk* disk, XCopyFloppy* floppy)
{
    _version = version;
    _esp = esp;
    _config = config;
    _disk = disk;
    _floppy = floppy;

    _editor.begin(this, onEditorLine, onEditorComplete, writeConsole);
    _completer.begin(listDirectory);

    // What DF0: reads through. The console is the only thing that mounts it, and
    // until this is called the floppy driver refuses to open - so a mount with no
    // drive attached fails at the door rather than through a null pointer.
    xcopyAdfFloppyAttach(_disk, _floppy, _config->getRetryCount());
}

void XCopyCommandLine::onEditorLine(void *caller, const String &line)
{
    XCopyCommandLine *self = (XCopyCommandLine *)caller;
    self->doCommand(line);
    self->printPrompt();
}

void XCopyCommandLine::onEditorComplete(void *caller, uint8_t presses)
{
    XCopyCommandLine *self = (XCopyCommandLine *)caller;
    self->_completer.complete(self->_editor, presses);
}

// DISPATCH

/**
 * @brief Mount the SD card, reporting the reason if it will not.
 *
 * Was copy-pasted into eight handlers, each with its own spelling of the same
 * four checks, and two of them called begin() twice.
 */
static bool mountSdCard()
{
    XCopySDCard sdcard;

    if (!sdcard.cardDetect() || !sdcard.begin())
    {
        Log << sdcard.getError() << "\r\n";
        return false;
    }

    return true;
}

void XCopyCommandLine::doCommand(String command)
{
    /*
       Anything that moves the head or reads a track leaves the decoded track
       buffer holding something else, and DF0:'s driver caches which track is in
       there. One command is one operation, so forgetting between commands keeps
       the cache correct without giving up what it is for - a directory listing is
       one command and gets one head pass per track, not eleven.
    */
    xcopyAdfFloppyInvalidate();

    // Arduino's char/char replace substitutes bytes without changing the length, so
    // the previous replace((char)10, (char)0) pair embedded NULs instead of removing
    // anything. Replacing with an empty String actually shortens it.
    command.replace("\r", "");
    command.replace("\n", "");
    command.trim();

    if (command.length() == 0)
        return;

    // The command word, and the rest of the line for XCopyArgs. Split here rather
    // than in the tokenizer so a raw tail command keeps its spacing exactly.
    String name = command;
    String tail = "";
    const int space = command.indexOf(' ');
    if (space > 0)
    {
        name = command.substring(0, space);
        tail = command.substring(space + 1);
    }

    const XCopyCommandDef *def = xcopyFindCommand(name);
    if (def == nullptr)
    {
        Log << "Unknown command: '" << name << "'. Type 'help' for a list.\r\n";
        return;
    }

    String error;
    XCopyArgs args;
    if (!args.parse(def, tail, error))
    {
        Log << XCopyConsole::error(error) << "\r\n";
        Log << "Try 'help " << def->name << "'\r\n";
        return;
    }

    /*
       The two preconditions that used to open most handlers. Checked from the
       command's flags, before the handler runs, so there is one wording of each
       and no handler can forget one - "writeflash" never had the disk check that
       every other write command does.
    */
    if ((def->flags & XCOPY_NEEDS_DISK) && !_floppy->diskChange())
    {
        Log << F("Disk not inserted into floppy\r\n");
        return;
    }

    if ((def->flags & XCOPY_NEEDS_SD) && !mountSdCard())
        return;

    dispatch(def, args);
}

void XCopyCommandLine::dispatch(const XCopyCommandDef *command, const XCopyArgs &args)
{
    switch (command->id)
    {
    case XCopyCmd::help:       cmdHelp(args);       break;
    case XCopyCmd::version:    cmdVersion();        break;
    case XCopyCmd::clear:      cmdClear();          break;
    case XCopyCmd::reboot:     cmdReboot();         break;
    case XCopyCmd::config:     cmdConfig();         break;
    case XCopyCmd::mem:        cmdMem();            break;

    case XCopyCmd::dir:        cmdDir(args);        break;
    case XCopyCmd::cat:        cmdCat(args);        break;
    case XCopyCmd::rm:         cmdRm(args);         break;
    case XCopyCmd::md5:        cmdMd5(args);        break;
    case XCopyCmd::cp:         cmdCp(args);         break;
    case XCopyCmd::mkdir:      cmdMkdir(args);      break;
    case XCopyCmd::mount:      cmdMount(args);      break;
    case XCopyCmd::unmount:    cmdUnmount(args);    break;

    case XCopyCmd::readadf:    cmdReadAdf(args);    break;
    case XCopyCmd::writeadf:   cmdWriteAdf(args);   break;
    case XCopyCmd::readscp:    cmdReadScp(args);    break;
    case XCopyCmd::writeflash: cmdWriteFlash();     break;
    case XCopyCmd::writebin:   cmdWriteBin(args);   break;
    case XCopyCmd::live:       cmdLive();           break;
    case XCopyCmd::testdisk:   cmdTestDisk();       break;
    case XCopyCmd::scanblocks: cmdScanBlocks();     break;
    case XCopyCmd::search:     cmdSearch(args);     break;
    case XCopyCmd::modsearch:  cmdModSearch();      break;
    case XCopyCmd::modrip:     cmdModRip(args);     break;

    case XCopyCmd::boot:       cmdBoot(args);       break;
    case XCopyCmd::hist:       cmdHist();           break;
    case XCopyCmd::rpm:        cmdRpm(args);        break;
    case XCopyCmd::headcal:    cmdHeadCal(args);    break;
    case XCopyCmd::diskinfo:   cmdDiskInfo(args);   break;
    case XCopyCmd::drivetoolkit: cmdDriveToolkit();  break;
    case XCopyCmd::name:       cmdName();           break;
    case XCopyCmd::print:      cmdPrint();          break;
    case XCopyCmd::read:       cmdRead(args);       break;
    case XCopyCmd::dump:       cmdDump(args);       break;
    case XCopyCmd::vol:        cmdVol(args);        break;
    case XCopyCmd::weak:       cmdWeak();           break;

    case XCopyCmd::time:       cmdTime();           break;
    case XCopyCmd::settime:    cmdSetTime(args);    break;
    case XCopyCmd::timezone:   cmdTimeZone(args);   break;

    case XCopyCmd::connect:    cmdConnect(args);    break;
    case XCopyCmd::clearwifi:  cmdClearWifi();      break;
    case XCopyCmd::status:     espQuery("status");  break;
    case XCopyCmd::ip:         espQuery("ip");      break;
    case XCopyCmd::mac:        espQuery("mac");     break;
    case XCopyCmd::ssid:       espQuery("ssid");    break;
    case XCopyCmd::rssi:       espQuery("rssi");    break;
    case XCopyCmd::websocket:  cmdWebsocket(args);  break;
    case XCopyCmd::scan:       cmdScan();           break;
    case XCopyCmd::ping:       espQuery("ping", 5000); break;
    case XCopyCmd::pass:       cmdPass();           break;

    default:
        break;
    }
}

// HELP

String XCopyCommandLine::helpSignature(const XCopyCommandDef *command)
{
    String line = command->name;

    if (command->alias != nullptr)
    {
        line += " | ";
        line += command->alias;
    }

    if (command->subject != XCopyArgKind::none && command->subjectName != nullptr)
    {
        line += " <";
        line += command->subjectName;
        line += ">";
    }

    // Not the options themselves: "readscp -cyls <text> -revs <n> -file <path>" is
    // wider than the column and would be truncated into a lie. This says there are
    // some, and "help readscp" lists them.
    if (command->optionCount > 0)
        line += " [-options]";

    return line;
}

void XCopyCommandLine::printHelp()
{
    helpRule('.', '-', '-', '.');
    helpWide("X-Copy Standalone " + _version);
    helpRule('|', '-', '-', '|');
    helpRow("Command", "Description");

    for (uint8_t category = 0; category < (uint8_t)XCopyCat::count; category++)
    {
        helpRule('|', '-', '+', '|');

        bool heading = false;
        for (uint8_t i = 0; i < XCOPY_COMMAND_COUNT; i++)
        {
            const XCopyCommandDef &entry = XCOPY_COMMANDS[i];
            if ((uint8_t)entry.category != category)
                continue;

            // Printed here rather than before the loop, so a category with nothing
            // in it leaves no empty heading behind.
            if (!heading)
            {
                helpWide(xcopyCategoryName(entry.category));
                helpRule('|', '-', '+', '|');
                heading = true;
            }

            helpRow(helpSignature(&entry), entry.help);
        }
    }

    helpRule('`', '-', '-', '\'');
    Log << F("Options are named: readscp -cyls 0-83 -revs 3 -file \"my disk.scp\"\r\n");
    Log << F("'help <command>' lists the options of one command.\r\n");
}

void XCopyCommandLine::printCommandHelp(const XCopyCommandDef *command)
{
    Log << XCopyConsole::bold_white() << command->name << XCopyConsole::reset();
    if (command->alias != nullptr)
        Log << " | " << command->alias;
    Log << F(" - ") << command->help << F("\r\n\r\n");

    Log << F("  usage: ") << helpSignature(command) << F("\r\n");

    if (command->subject != XCopyArgKind::none && command->subjectName != nullptr)
    {
        Log << F("    <") << command->subjectName << F("> ")
            << ((command->flags & XCOPY_SUBJECT_REQUIRED) ? F("(required) ") : F("(optional) "))
            << xcopyKindName(command->subject) << F("\r\n");
    }

    for (uint8_t i = 0; i < command->optionCount; i++)
    {
        const XCopyOption &option = command->options[i];
        String line = "    -";
        line += option.name;
        if (option.kind != XCopyArgKind::flag)
        {
            line += " ";
            line += (option.kind == XCopyArgKind::choice) ? String(option.choices) : String(xcopyKindName(option.kind));
        }
        Log << pad(line, 24) << option.help << F("\r\n");
    }

    if (command->flags & XCOPY_NEEDS_DISK)
        Log << F("  needs a disk in the drive\r\n");
    if (command->flags & XCOPY_NEEDS_SD)
        Log << F("  needs an SD card\r\n");
}

void XCopyCommandLine::cmdHelp(const XCopyArgs &args)
{
    if (!args.hasSubject())
    {
        printHelp();
        return;
    }

    const XCopyCommandDef *command = xcopyFindCommand(args.subject());
    if (command == nullptr)
    {
        Log << "Unknown command: '" << args.subject() << "'\r\n";
        return;
    }

    printCommandHelp(command);
}

// GENERAL

void XCopyCommandLine::cmdVersion()
{
    Log << F("Version: ") << _version << F("\r\n");
}

void XCopyCommandLine::cmdClear()
{
    Log << XCopyConsole::clearscreen() << XCopyConsole::home();
}

void XCopyCommandLine::cmdReboot()
{
    _callback(_caller, "rebootDevice");
}

void XCopyCommandLine::cmdConfig()
{
    _config->dumpConfig();
}

void XCopyCommandLine::cmdMem()
{
    uint32_t stackTop;
    uint32_t heapTop;

    // current position of the stack.
    stackTop = (uint32_t) &stackTop;

    // current position of heap.
    void* hTop = malloc(1);
    heapTop = (uint32_t) hTop;
    free(hTop);

    char sStackTop[12];
    char sHeapTop[12];

    sprintf(sStackTop, "0x%08" PRIx32, stackTop);
    sprintf(sHeapTop, "0x%08" PRIx32,  heapTop);

    // The difference is (approximately) the free, available ram.
    Log << F("Stack Top: ") << sStackTop << F("\r\n");
    Log << F("Heap Top: ") << sHeapTop << F("\r\n");
    Log << F("Free: ") << (stackTop - heapTop) << F(" bytes free\r\n");
}

// SD CARD

void XCopyCommandLine::cmdDir(const XCopyArgs &args)
{
    setBusy(true);

    /*
       One command for the card and for a mounted image. The path says which:
       "dir /adfs" and "dir SD:/adfs" list the card, "dir ADF0:c" lists inside an
       image. Adding a second command for the second case would have meant two
       spellings of the same idea and a completer that had to know which was which.
    */
    XCopyAdfMount::Slot *slot = nullptr;
    String within;
    if (XCopyAdfMount::resolve(args.subject(), slot, within))
    {
        if (slot == nullptr)
            printDirectory(within);
        else
            listVolume(*slot, within);
    }

    setBusy(false);
}

void XCopyCommandLine::cmdCat(const XCopyArgs &args)
{
    XCopyAdfMount::Slot *slot = nullptr;
    String path;
    if (!XCopyAdfMount::resolve(args.subject(), slot, path))
        return;

    if (slot != nullptr)
    {
        catVolume(*slot, path);
        return;
    }

    FatFile file;
    if (!file.open(path.c_str()))
    {
        Log << F("unable to open: '") + path + F("'\r\n");
        return;
    }

    const size_t bufferSize = 512;
    XCopyScratch::Guard scratch("command.dump", bufferSize);
    if (!scratch.valid())
    {
        Log << F("track buffer busy\r\n");
        file.close();
        return;
    }
    char *buffer = (char *)scratch.get();

    // read() returns -1 on error; the old loop tested readsize only after using
    // it, so a failed read appended garbage and then looped forever on (size_t)-1.
    int readsize = 0;
    while ((readsize = file.read(buffer, bufferSize)) > 0)
    {
        String line = "";
        for (int i = 0; i < readsize; i++)
        {
            line.append(buffer[i]);
        }
        Log << line;
    }

    file.close();

    Log << F("[-- eof]\r\n");
}

void XCopyCommandLine::cmdRm(const XCopyArgs &args)
{
    XCopyAdfMount::Slot *slot = nullptr;
    String path;
    if (!XCopyAdfMount::resolve(args.subject(), slot, path))
        return;

    if (slot == nullptr)
    {
        XCopySDCard sdcard;
        if (sdcard.deleteFile(path))
            Log << "'" + path + F("' deleted\r\n");
        else
            Log << F("unable to delete: '") + path + F("'\r\n");
        return;
    }

    if (!writableVolume(*slot))
        return;

    String leaf;
    if (!XCopyAdfMount::walkTo(*slot, path, leaf))
        return;

    if (leaf.length() == 0)
    {
        Log << XCopyConsole::error("rm needs a name") << F("\r\n");
        return;
    }

    /*
       adfRemoveEntry() refuses a directory that is not empty, which is the
       behaviour to want: there is no undo on a floppy, and a recursive delete that
       went wrong would take the disk with it.
    */
    XCopyAdf::clearErrors();
    if (adfRemoveEntry(slot->vol, slot->vol->curDirPtr, leaf.c_str()) != ADF_RC_OK)
    {
        Log << XCopyConsole::error("unable to delete '" + leaf + "' from " +
                                   String(slot->name) + ":")
            << F("\r\n");
        return;
    }

    Log << slot->name << F(":") << path << F(" deleted\r\n");
}

void XCopyCommandLine::cmdMd5(const XCopyArgs &args)
{
    /*
       One of the two, never both and never neither. This was a positional that
       meant a filename unless it happened to spell "flash", so a file called
       flash could not be hashed and a typo hashed the wrong thing silently.
    */
    if (args.has("flash"))
    {
        Log << _disk->flashToMD5() + "\r\n";
        return;
    }

    if (!args.hasSubject())
    {
        Log << F("md5 needs a file, or -flash\r\n");
        return;
    }

    if (!mountSdCard())
        return;

    XCopySDCard sdcard;
    const String &path = args.subject();

    if (!sdcard.fileExists(path))
    {
        Log << "File not found: '" + path + "'\r\n";
        return;
    }

    Log << _disk->adfToMD5(path) + "\r\n";
}

// FILE MANAGEMENT

/*
   How much malloc arena a copy needs before it should be started.

   An open AdfFile is about 1,600 bytes - a file header block, a data block, an
   extension block and the handle - and a copy between two mounted volumes has two
   of them open at once. Finding that out half way through means a failed
   allocation inside adfFileWrite(), which leaves a partial file and a bitmap that
   has already been changed.

   Checking first turns that into a refusal. The number is per open ADF file plus
   a few hundred bytes for the Strings the console builds while it reports.
*/
static const uint32_t kHeapPerOpenFile = 1700;
static const uint32_t kHeapSlack = 600;

bool XCopyCommandLine::heapAllows(uint8_t openAdfFiles)
{
    const uint32_t need = (uint32_t)openAdfFiles * kHeapPerOpenFile + kHeapSlack;
    const uint32_t have = XCopyAdfMount::freeHeap();

    if (have >= need)
        return true;

    Log << XCopyConsole::error("not enough memory: " + String(have) +
                               " bytes free, " + String(need) + " needed")
        << F("\r\n");
    Log << F("unmount a slot and try again\r\n");
    return false;
}

/*
   Where a copy is going, worked out once for both kinds of destination.

   A destination that ends in a slash, or is nothing at all, is a directory and the
   file keeps the name it had. Anything else names the file itself. That is the one
   rule, and it is the rule because guessing - looking to see whether the last
   component happens to be an existing directory - makes "cp a -to b" mean two
   different things depending on what is already there.
*/
static void copyDestination(const String &given, const String &sourceLeaf,
                            String &directory, String &leaf)
{
    if (given.length() == 0 || given.charAt(given.length() - 1) == '/')
    {
        directory = given;
        leaf = sourceLeaf;
        return;
    }

    xcopySplitLeaf(given, directory, leaf);
    if (directory.length() > 0)
        directory += "/";
}

bool XCopyCommandLine::writableVolume(XCopyAdfMount::Slot &slot)
{
    if (slot.dev->readOnly || slot.vol->readOnly)
    {
        Log << XCopyConsole::error(String(slot.name) + ": is mounted read only") << F("\r\n");
        if (slot.drive)
            Log << F("the drive is read only; use readadf to take an image of it\r\n");
        else
            Log << F("remount it with -rw\r\n");
        return false;
    }
    return true;
}

void XCopyCommandLine::cmdCp(const XCopyArgs &args)
{
    if (!args.has("to"))
    {
        Log << F("cp needs a destination: cp <file> -to <where>\r\n");
        return;
    }

    XCopyAdfMount::Slot *fromSlot = nullptr;
    String fromPath;
    if (!XCopyAdfMount::resolve(args.subject(), fromSlot, fromPath))
        return;

    XCopyAdfMount::Slot *toSlot = nullptr;
    String toPath;
    if (!XCopyAdfMount::resolve(args.text("to"), toSlot, toPath))
        return;

    String fromDirectory, fromLeaf;
    xcopySplitLeaf(fromPath, fromDirectory, fromLeaf);
    if (fromLeaf.length() == 0)
    {
        Log << XCopyConsole::error("cp needs a file, not a directory") << F("\r\n");
        return;
    }

    String toDirectory, toLeaf;
    copyDestination(toPath, fromLeaf, toDirectory, toLeaf);

    const uint8_t adfSides = (fromSlot != nullptr ? 1 : 0) + (toSlot != nullptr ? 1 : 0);
    if (adfSides > 0 && !heapAllows(adfSides))
        return;

    if (toSlot != nullptr && !writableVolume(*toSlot))
        return;

    /*
       4KB rather than 512.

       Every round of the loop is a read and a write, and on a floppy each of those
       may be a whole track. Eight blocks at a time is eight times fewer of them,
       and the buffer is borrowed from the track buffer so the size costs nothing
       that was not already allocated.
    */
    const size_t bufferSize = 4096;
    XCopyScratch::Guard scratch("command.cp", bufferSize);
    if (!scratch.valid())
    {
        Log << F("track buffer busy\r\n");
        return;
    }
    uint8_t *buffer = scratch.get();

    setBusy(true);
    unsigned long copied = 0;
    bool ok = false;

    if (fromSlot != nullptr && toSlot != nullptr)
    {
        /*
           Both sides walked before either file is opened.

           walkTo() moves a volume's own current directory, and when the source and
           the destination are the same volume the second walk would move the first
           one out from under it. Doing both first and reading the sector numbers
           back is what makes "cp ADF0:c/list -to ADF0:s/" work.
        */
        String unusedLeaf;
        if (XCopyAdfMount::walkTo(*fromSlot, fromPath, unusedLeaf))
        {
            const ADF_SECTNUM fromDir = fromSlot->vol->curDirPtr;

            if (XCopyAdfMount::walkTo(*toSlot, toDirectory + toLeaf, unusedLeaf))
            {
                const ADF_SECTNUM toDir = toSlot->vol->curDirPtr;
                fromSlot->vol->curDirPtr = fromDir;
                toSlot->vol->curDirPtr = toDir;

                const AdfCopyResult result =
                    adfCopyFile(fromSlot->vol, fromLeaf.c_str(),
                                toSlot->vol, toLeaf.c_str(),
                                buffer, bufferSize, &copied);
                ok = (result == ADF_COPY_OK);
                if (!ok)
                    Log << XCopyConsole::error(adfCopyResultText(result)) << F("\r\n");
            }
        }
    }
    else if (fromSlot == nullptr && toSlot != nullptr)
    {
        ok = copyCardToVolume(fromPath, *toSlot, toDirectory, toLeaf,
                              buffer, bufferSize, copied);
    }
    else if (fromSlot != nullptr && toSlot == nullptr)
    {
        ok = copyVolumeToCard(*fromSlot, fromPath, fromLeaf, toDirectory + toLeaf,
                              buffer, bufferSize, copied);
    }
    else
    {
        ok = copyCardToCard(fromPath, toDirectory + toLeaf, buffer, bufferSize, copied);
    }

    setBusy(false);

    if (ok)
        Log << XCopyConsole::success(String(copied) + " bytes copied to " + toLeaf)
            << F("\r\n");
    else if (copied > 0)
        Log << XCopyConsole::error(String(copied) + " bytes were written before it stopped")
            << F("\r\n");
}

bool XCopyCommandLine::copyCardToVolume(const String &fromPath,
                                        XCopyAdfMount::Slot &toSlot,
                                        const String &toDirectory,
                                        const String &toLeaf,
                                        uint8_t *buffer, size_t bufferSize,
                                        unsigned long &copied)
{
    FatFile in;
    if (!in.open(fromPath.c_str(), O_RDONLY))
    {
        Log << XCopyConsole::error("unable to open '" + fromPath + "'") << F("\r\n");
        return false;
    }

    String unusedLeaf;
    if (!XCopyAdfMount::walkTo(toSlot, toDirectory + toLeaf, unusedLeaf))
    {
        in.close();
        return false;
    }

    if (adfGetEntryBlockNum(toSlot.vol, toSlot.vol->curDirPtr, toLeaf.c_str()) != -1)
    {
        Log << XCopyConsole::error("'" + toLeaf + "' is already in " +
                                   String(toSlot.name) + ":")
            << F("\r\n");
        in.close();
        return false;
    }

    struct AdfFile *out = adfFileOpen(toSlot.vol, toLeaf.c_str(), ADF_FILE_MODE_WRITE);
    if (out == NULL)
    {
        Log << XCopyConsole::error("unable to create '" + toLeaf + "'") << F("\r\n");
        in.close();
        return false;
    }

    bool ok = true;
    int got = 0;
    while ((got = in.read(buffer, bufferSize)) > 0)
    {
        if (adfFileWrite(out, (uint32_t)got, buffer) != (uint32_t)got)
        {
            Log << XCopyConsole::error(String(toSlot.name) + ": ran out of room") << F("\r\n");
            ok = false;
            break;
        }
        copied += (unsigned long)got;
    }

    if (got < 0)
    {
        Log << XCopyConsole::error("the card stopped reading part way through") << F("\r\n");
        ok = false;
    }

    if (ok && adfFileFlush(out) != ADF_RC_OK)
    {
        Log << XCopyConsole::error("the last block could not be written") << F("\r\n");
        ok = false;
    }

    adfFileClose(out);
    in.close();
    return ok;
}

bool XCopyCommandLine::copyVolumeToCard(XCopyAdfMount::Slot &fromSlot,
                                        const String &fromPath,
                                        const String &fromLeaf,
                                        const String &toPath,
                                        uint8_t *buffer, size_t bufferSize,
                                        unsigned long &copied)
{
    String unusedLeaf;
    if (!XCopyAdfMount::walkTo(fromSlot, fromPath, unusedLeaf))
        return false;

    struct AdfFile *in = adfFileOpen(fromSlot.vol, fromLeaf.c_str(), ADF_FILE_MODE_READ);
    if (in == NULL)
    {
        Log << XCopyConsole::error("unable to open '" + fromLeaf + "' in " +
                                   String(fromSlot.name) + ":")
            << F("\r\n");
        return false;
    }

    if (xcopySd().exists(toPath.c_str()))
    {
        Log << XCopyConsole::error("'" + toPath + "' is already on the card") << F("\r\n");
        adfFileClose(in);
        return false;
    }

    FatFile out;
    if (!out.open(toPath.c_str(), O_RDWR | O_CREAT | O_TRUNC))
    {
        Log << XCopyConsole::error("unable to create '" + toPath + "'") << F("\r\n");
        adfFileClose(in);
        return false;
    }

    bool ok = true;
    while (!adfFileAtEOF(in))
    {
        const uint32_t got = adfFileRead(in, (uint32_t)bufferSize, buffer);
        if (got == 0)
        {
            Log << XCopyConsole::error("the image stopped reading part way through") << F("\r\n");
            ok = false;
            break;
        }

        if (out.write(buffer, got) != (int)got)
        {
            Log << XCopyConsole::error("the card ran out of room") << F("\r\n");
            ok = false;
            break;
        }
        copied += got;
    }

    if (!out.sync())
    {
        Log << XCopyConsole::error("the card would not flush") << F("\r\n");
        ok = false;
    }

    out.close();
    adfFileClose(in);
    return ok;
}

bool XCopyCommandLine::copyCardToCard(const String &fromPath, const String &toPath,
                                      uint8_t *buffer, size_t bufferSize,
                                      unsigned long &copied)
{
    if (xcopySd().exists(toPath.c_str()))
    {
        Log << XCopyConsole::error("'" + toPath + "' is already on the card") << F("\r\n");
        return false;
    }

    FatFile in;
    if (!in.open(fromPath.c_str(), O_RDONLY))
    {
        Log << XCopyConsole::error("unable to open '" + fromPath + "'") << F("\r\n");
        return false;
    }

    FatFile out;
    if (!out.open(toPath.c_str(), O_RDWR | O_CREAT | O_TRUNC))
    {
        Log << XCopyConsole::error("unable to create '" + toPath + "'") << F("\r\n");
        in.close();
        return false;
    }

    bool ok = true;
    int got = 0;
    while ((got = in.read(buffer, bufferSize)) > 0)
    {
        if (out.write(buffer, got) != got)
        {
            Log << XCopyConsole::error("the card ran out of room") << F("\r\n");
            ok = false;
            break;
        }
        copied += (unsigned long)got;
    }

    if (got < 0)
    {
        Log << XCopyConsole::error("the card stopped reading part way through") << F("\r\n");
        ok = false;
    }

    if (!out.sync())
        ok = false;

    out.close();
    in.close();
    return ok;
}

void XCopyCommandLine::cmdMkdir(const XCopyArgs &args)
{
    XCopyAdfMount::Slot *slot = nullptr;
    String path;
    if (!XCopyAdfMount::resolve(args.subject(), slot, path))
        return;

    if (slot == nullptr)
    {
        // SdFat makes the whole path, which is the useful behaviour for a card
        // where directories are cheap and nesting is how anyone organises ADFs.
        if (xcopySd().mkdir(path.c_str(), true))
            Log << "'" + path + F("' created\r\n");
        else
            Log << XCopyConsole::error("unable to create '" + path + "'") << F("\r\n");
        return;
    }

    if (!writableVolume(*slot))
        return;

    String leaf;
    if (!XCopyAdfMount::walkTo(*slot, path, leaf))
        return;

    if (leaf.length() == 0)
    {
        Log << XCopyConsole::error("mkdir needs a name") << F("\r\n");
        return;
    }

    XCopyAdf::clearErrors();
    if (adfCreateDir(slot->vol, slot->vol->curDirPtr, leaf.c_str()) != ADF_RC_OK)
    {
        Log << XCopyConsole::error("unable to create '" + leaf + "' in " +
                                   String(slot->name) + ":")
            << F("\r\n");
        return;
    }

    Log << slot->name << F(":") << path << F(" created\r\n");
}

// MOUNTED IMAGES

void XCopyCommandLine::cmdMount(const XCopyArgs &args)
{
    XCopyAdfMount::begin();
    XCopyAdfMount::Slot *slots = XCopyAdfMount::slots();

    if (!args.hasSubject())
    {
        for (uint8_t i = 0; i < XCopyAdfMount::kSlots; i++)
        {
            Log << slots[i].name << F(":  ");
            if (!slots[i].mounted())
            {
                Log << (slots[i].drive ? F("-  (the drive)\r\n") : F("-\r\n"));
                continue;
            }

            Log << (slots[i].vol->volName ? slots[i].vol->volName : "?");
            Log << F("  (")
                << (slots[i].drive ? String("the disk in the drive") : slots[i].path)
                << F(")");
            Log << (slots[i].dev->readOnly ? F("  read only\r\n") : F("  read write\r\n"));
        }

        // Printed with the table because a mount is not free - roughly 720 bytes
        // for the volume, another 1,600 while a file inside it is open - and this
        // is the number that says whether the next one will fit.
        Log << XCopyAdfMount::freeHeap() << F(" bytes of heap free\r\n");
        return;
    }

    /*
       "mount df0:" is the drive, not a file called df0. It is the one subject that
       names a device instead of a path, because the drive has no backing file to
       name - what is in it is whatever the operator put there.
    */
    XCopyPath named;
    xcopySplitPath(args.subject(), named);

    /*
       The colon is what says "device", but "mount df0" without one is what an
       Amiga habit produces and refusing it would be pedantry. A bare name is
       taken as a device only when it matches a drive slot, so a file called
       "adf0" still mounts; one actually called "df0" can be named SD:df0.
    */
    XCopyAdfMount::Slot *bare = named.qualified ? nullptr
                                                : XCopyAdfMount::find(args.subject());
    if (bare != nullptr && !bare->drive)
        bare = nullptr;

    if (bare != nullptr || (named.qualified && !named.isCard()))
    {
        const String device = bare != nullptr ? String(bare->name) : named.device;
        XCopyAdfMount::Slot *drive = bare != nullptr ? bare
                                                     : XCopyAdfMount::find(named.device);
        if (drive == nullptr)
        {
            Log << XCopyConsole::error("no such device '" + named.device + ":'") << F("\r\n");
            return;
        }

        if (!drive->drive)
        {
            Log << XCopyConsole::error(named.device + ": needs a file to mount") << F("\r\n");
            Log << F("try: mount <file> -slot ") << named.device << F("\r\n");
            return;
        }

        if (!XCopyAdfMount::mountDrive(*drive))
            return;

        Log << drive->name << F(": ") << (drive->vol->volName ? drive->vol->volName : "?");
        Log << F("  (the disk in the drive)  read only\r\n");
        return;
    }

    XCopyAdfMount::Slot *slot = nullptr;

    if (args.has("slot"))
    {
        slot = XCopyAdfMount::find(args.text("slot"));
        if (slot == nullptr)
        {
            Log << XCopyConsole::error("no such slot '" + args.text("slot") + "'") << F("\r\n");
            return;
        }
    }
    else
    {
        // First free image slot, so the common case is "mount game.adf" and
        // nothing else. The drive is skipped: it takes no file, and choosing it
        // for someone who named one would be a surprising way to fail.
        for (uint8_t i = 0; i < XCopyAdfMount::kSlots && slot == nullptr; i++)
            if (!slots[i].drive && !slots[i].mounted())
                slot = &slots[i];

        if (slot == nullptr)
        {
            Log << XCopyConsole::error("every slot is in use") << F("\r\n");
            Log << F("unmount one, or say which with -slot\r\n");
            return;
        }
    }

    const String path = args.subject();
    if (!XCopyAdfMount::mount(*slot, path, args.has("rw")))
        return;

    Log << slot->name << F(": ") << (slot->vol->volName ? slot->vol->volName : "?");
    Log << F("  (") << path << F(")");
    Log << (slot->dev->readOnly ? F("  read only\r\n") : F("  read write\r\n"));
}

void XCopyCommandLine::cmdUnmount(const XCopyArgs &args)
{
    if (!args.hasSubject())
    {
        XCopyAdfMount::unmountAll();
        Log << F("all slots released\r\n");
        return;
    }

    // The colon is optional here, because "unmount adf0:" is what anyone who has
    // just typed a path will reach for and refusing it would be pedantry.
    XCopyPath path;
    xcopySplitPath(args.subject(), path);
    const String name = path.qualified ? path.device : args.subject();

    XCopyAdfMount::Slot *slot = XCopyAdfMount::find(name);
    if (slot == nullptr)
    {
        Log << XCopyConsole::error("no such slot '" + args.subject() + "'") << F("\r\n");
        return;
    }

    if (!slot->mounted())
    {
        Log << slot->name << F(": already holds nothing\r\n");
        return;
    }

    XCopyAdfMount::unmount(*slot);
    Log << slot->name << F(": released\r\n");
}

void XCopyCommandLine::listVolume(XCopyAdfMount::Slot &slot, const String &within)
{
    /*
       The whole path is a directory here, not a directory and a leaf: "dir ADF0:c"
       means list c, not list the root and look for c in it. walkTo() splits off a
       leaf, so the trailing slash makes the whole of it the directory part.
    */
    String leaf;
    String directory = within;
    if (directory.length() > 0 && directory.charAt(directory.length() - 1) != '/')
        directory += "/";

    if (!XCopyAdfMount::walkTo(slot, directory, leaf))
        return;

    Log << F("Directory: ") << slot.name << F(":") << within << F("\r\n");
    XCopyAdfView::printListHeader();

    const uint16_t listed = XCopyAdfView::printDirectory(slot.vol, slot.vol->curDirPtr);
    Log << listed << (listed == 1 ? F(" entry\r\n") : F(" entries\r\n"));
}

void XCopyCommandLine::catVolume(XCopyAdfMount::Slot &slot, const String &within)
{
    String leaf;
    if (!XCopyAdfMount::walkTo(slot, within, leaf))
        return;

    if (leaf.length() == 0)
    {
        Log << XCopyConsole::error("cat needs a file, not a directory") << F("\r\n");
        return;
    }

    XCopyAdf::clearErrors();
    struct AdfFile *file = adfFileOpen(slot.vol, leaf.c_str(), ADF_FILE_MODE_READ);
    if (file == NULL)
    {
        Log << XCopyConsole::error("unable to open '" + leaf + "' in " +
                                   String(slot.name) + ":")
            << F("\r\n");
        return;
    }

    /*
       Read through the track buffer rather than a local.

       An open AdfFile already costs about 1,600 bytes of heap - three block
       buffers and a handle - and a 512 byte read buffer on top of that is worth
       borrowing rather than finding. If the buffer is busy, say so and stop:
       shrinking the read to something that fits on the stack would work and would
       also mean the one path that is slow is the one nobody notices is slow.
    */
    const size_t bufferSize = 512;
    XCopyScratch::Guard scratch("command.cat", bufferSize);
    if (!scratch.valid())
    {
        Log << F("track buffer busy\r\n");
        adfFileClose(file);
        return;
    }
    uint8_t *buffer = scratch.get();

    while (!adfFileAtEOF(file))
    {
        const uint32_t got = adfFileRead(file, bufferSize, buffer);
        if (got == 0)
            break;

        String line = "";
        for (uint32_t i = 0; i < got; i++)
            line.append((char)buffer[i]);
        Log << line;
    }

    adfFileClose(file);
    Log << F("[-- eof]\r\n");
}

// FLOPPY DISK

void XCopyCommandLine::cmdReadAdf(const XCopyArgs &args)
{
    // No filename given: diskToADF() names the file after the disk label and
    // the current date & time, the same as the menu and the web UI do.
    String path = args.text("file");

    if (path != "")
    {
        // On a copy: toLowerCase() mutates in place and path is the destination
        // path, which has to keep the case the user typed.
        String extension = path;
        if (!extension.toLowerCase().endsWith(".adf"))
        {
            Log << F("The file must be an ADF file\r\n");
            return;
        }

        // A bare filename lands in the ADF folder alongside the generated ones;
        // diskToADF() creates that directory if it is missing.
        if (path.indexOf("/") == -1)
            path = "/" + String(SD_ADF_PATH) + "/" + path;
    }

    _callback(_caller, "copyDiskToADF," + path);
}

void XCopyCommandLine::cmdWriteAdf(const XCopyArgs &args)
{
    XCopySDCard sdcard;
    const String &path = args.subject();

    if (!sdcard.fileExists(path))
    {
        Log << F("file does not exist\r\n");
        return;
    }

    String extension = path;
    if (!extension.toLowerCase().endsWith(".adf"))
    {
        Log << F("The file must be an ADF file\r\n");
        return;
    }

    _callback(_caller, "writeADFFile," + path);
}

/*
   Parse a "<first>-<last>" cylinder range.

   The range is the one value still parsed by shape rather than named, because
   "0-83" is one token and not two. Shared by readscp and diskinfo so the two
   cannot come to different conclusions about what a valid range is, and so an
   operator gets the same complaint about a bad one either way.

   An empty range is not an error: it leaves first and last alone, so whatever
   defaults the caller set stand.

   @result false when a range was given and was malformed, having already said so.
*/
static bool parseCylinderRange(const String &range, uint8_t &first, uint8_t &last)
{
    if (range == "")
        return true;

    const int dash = range.indexOf('-');
    bool valid = dash > 0 && dash < (int)range.length() - 1;
    for (unsigned int i = 0; valid && i < range.length(); i++)
        if ((int)i != dash && !isDigit(range.charAt(i)))
            valid = false;

    if (!valid)
    {
        Log << F("-cyls must be a range, <first>-<last>\r\n");
        return false;
    }

    first = (uint8_t)range.substring(0, dash).toInt();
    last = (uint8_t)range.substring(dash + 1).toInt();

    if (last >= MAX_CYLINDERS || first > last)
    {
        Log << F("Cylinder range must be within 0-") << (MAX_CYLINDERS - 1)
            << F(", lowest first\r\n");
        return false;
    }
    return true;
}

void XCopyCommandLine::cmdReadScp(const XCopyArgs &args)
{
    uint8_t firstCylinder = 0;
    uint8_t lastCylinder = 0;
    uint8_t revolutions = 0;

    /*
       The range is the one value that is still parsed by shape, because "0-83" is
       one value and not two. Everything around it that used to be sniffed - is
       this token a revolution count, or the first word of a filename with spaces
       in it - is now named, so the sniffing cannot reach the filename any more.
    */
    if (!parseCylinderRange(args.text("cyls"), firstCylinder, lastCylinder))
        return;

    if (args.has("revs"))
    {
        revolutions = (uint8_t)args.number("revs", 0);

        if (revolutions < 1 || revolutions > SCP_MAX_REVS)
        {
            Log << F("Revolutions must be 1-") << SCP_MAX_REVS << F("\r\n");
            return;
        }
    }

    String filename = args.text("file");

    if (filename != "")
    {
        // On a copy: toLowerCase() mutates in place and filename is the
        // destination path, which has to keep the case the user typed.
        String extension = filename;
        if (!extension.toLowerCase().endsWith(".scp"))
        {
            Log << F("The file must be an SCP file\r\n");
            return;
        }

        // A bare filename lands in the SCP folder alongside the generated ones;
        // diskToSCP() creates that directory if it is missing.
        if (filename.indexOf("/") == -1)
            filename = "/" + String(SD_SCP_PATH) + "/" + filename;
    }

    // "<first>-<last>,<revs>,<path>", with the path last because a filename may
    // contain a comma and the two numeric fields never can. Zero means "not
    // given" and the saved setting applies.
    _callback(_caller, "copyDiskToSCP," + String(firstCylinder) + "-" + String(lastCylinder) +
                           "," + String(revolutions) + "," + filename);
}

void XCopyCommandLine::cmdWriteFlash()
{
    // onWebCommand() matches "copyDiskToFlash"; the old "copyDisktoFlash"
    // spelling fell through every branch and the command did nothing.
    _callback(_caller, "copyDiskToFlash");
}

void XCopyCommandLine::cmdWriteBin(const XCopyArgs &args)
{
    if (!args.has("file") || !args.has("block"))
    {
        Log << F("writebin needs -file and -block\r\n");
        return;
    }

    setBusy(true);
    _disk->writeFileToBlocks(args.text("file"), (int)args.number("block", 0), _config->getRetryCount());
    setBusy(false);
}

void XCopyCommandLine::cmdLive()
{
    /*
       Hands this USB session to XCopyLive, which switches it to the binary protocol
       in shared/XCopyLiveProtocol.h. Everything after the banner XCopyLive prints
       is frames, so nothing may print here on the way in.
    */
    _callback(_caller, "liveStream");
}

void XCopyCommandLine::cmdTestDisk()
{
    _callback(_caller, "testDisk");
}

void XCopyCommandLine::cmdScanBlocks()
{
    _callback(_caller, "scanBlocks");
}

void XCopyCommandLine::cmdSearch(const XCopyArgs &args)
{
    _callback(_caller, "asciiSearch," + args.subject());
}

void XCopyCommandLine::cmdModSearch()
{
    _callback(_caller, "modSearch");
}

void XCopyCommandLine::cmdModRip(const XCopyArgs &args)
{
    if (!args.has("block") || !args.has("offset") || !args.has("size"))
    {
        Log << F("modrip needs -block, -offset and -size\r\n");
        return;
    }

    const int block = (int)args.number("block", 0);
    const int offset = (int)args.number("offset", 0);
    const int size = (int)args.number("size", 0);

    // Checked before setBusy(), not after. The old order took the busy pin and
    // then returned on each of these without giving it back, so a mistyped modrip
    // left the whole device wedged as busy.
    if (block > 1759)
    {
        Log << F("Error: -block must be less than 1759.\r\n");
        return;
    }

    if (offset >= 512)
    {
        Log << F("Error: -offset must be less than 512 bytes.\r\n");
        return;
    }

    if (size <= 0)
    {
        Log << F("Error: -size must be greater than 0 bytes.\r\n");
        return;
    }

    setBusy(true);

    DiskLocation dl;
    dl.setBlock(block);
    if (_disk->modRip(dl, offset, size, _config->getRetryCount()))
        Log << F("Mod file written successfully\r\n");
    else
        Log << F("Writing mod file failed\r\n");

    setBusy(false);
}

// ANALYSIS

void XCopyCommandLine::readTrackFromFlash(uint16_t track)
{
    SerialFlashFile flashFile = SerialFlash.open("DISKCOPY.TMP");
    flashFile.seek(track * 11 * 512);

    for (uint8_t i = 0; i < 11; i++)
    {
        // Straight into the sector. The old code read into a 512 byte local and
        // then byte copied it across, which cost a frame this deep in doCommand()
        // and bought nothing - the destination is already contiguous and exactly
        // this size.
        struct Sector *aSec = (Sector *)&_floppy->getTrack()[i].sector[0];
        flashFile.read(aSec->data, sizeof(aSec->data));
    }
    _floppy->setSectorCnt(11);
}

void XCopyCommandLine::cmdBoot(const XCopyArgs &args)
{
    Log.printf("Reading Track %d\r\n", 0);

    /*
       "boot -flash" is what "bootf" was supposed to be. What bootf actually did
       was rewrite its own command and parameter and then return, so it read
       nothing and printed nothing - it has been listed in the help and broken for
       as long as it has existed.
    */
    if (args.has("flash"))
    {
        readTrackFromFlash(0);
    }
    else
    {
        _floppy->gotoLogicTrack(0);
        // int, not uint8_t: readTrack() signals failure with -1.
        int errors = _floppy->readTrack(false);
        if (errors != -1)
        {
            Log << F("Sectors found: ") << _floppy->getSectorCnt() << F(" Errors found: ");
            Serial.print(errors, BIN);
            Log << F(" Track expected: 0 Track found: ") << _floppy->getTrackInfo()
                << F(" bitCount: ") << _floppy->getBitCount() << F(" (Read OK)\r\n");
        }
        else
        {
            Log << F("bitCount: ") << _floppy->getBitCount() << F(" (Read failed!)\r\n");
        }
    }

    _floppy->printBootSector();

    Log << F("\r\nScanning boot block for match ...\r\n");

    uint32_t crc32 = _floppy->bootSectorCRC32();
    Track *track = _floppy->getTrack();
    struct Sector *block0 = (Sector *)&track[0].sector;
    struct Sector *block1 = (Sector *)&track[0].sector;
    XCopyBrainFile::identifyBootblock(block0->data, block1->data, crc32);
}

void XCopyCommandLine::cmdHist()
{
    _floppy->analyseHist(false);
    _floppy->printHist();
}

void XCopyCommandLine::cmdRpm(const XCopyArgs &args)
{
    uint32_t interval = (uint32_t)args.number("interval", 1000);
    if (interval < 100) interval = 100;

    setBusy(true);
    _floppy->motorOn();
    // The newline that submitted this command is still queued, so the
    // wait-for-keypress loop below would exit before taking a reading.
    while (Serial.available()) Serial.read();
    _floppy->beginRPM();

    Log << F("Measuring drive speed, press any key to stop ...\r\n");

    uint32_t lastReading = millis() - interval;
    while (!Serial.available())
    {
        // motorTimeout() shuts the drive down after motorMaxTick idle
        // seconds; keep resetting the tick or it stops mid measurement
        _floppy->motorOn();

        if (millis() - lastReading < interval) continue;
        lastReading = millis();

        float rpm = _floppy->readRPM();
        if (rpm == 0.0f)
            Log << XCopyConsole::error(F("No index signal detected\r\n"));
        else
            Log << F("Drive speed: ") << twoDecimals(rpm) << F(" RPM\r\n");
    }
    while (Serial.available()) Serial.read();

    _floppy->endRPM();
    _floppy->motorOff();
    setBusy(false);
}

void XCopyCommandLine::cmdHeadCal(const XCopyArgs &args)
{
    // Starts the state and returns, like testdisk. Deliberately not the rpm
    // pattern of owning the console in a loop: that would starve the ESP link
    // and the TFT for as long as somebody was adjusting the drive.
    _callback(_caller, "headCalibration," + args.subject());
}

/*
   Analyse every track, from the drive or from an SCP image on the card.

   The table row carries neither XCOPY_NEEDS_DISK nor XCOPY_NEEDS_SD, which is the
   one place this command departs from the pattern the flags exist to enforce. It
   has to: -file analyses an image and wants no disk in the drive, while the drive
   form wants no card. A flag would demand both for both. The two checks are
   therefore here, worded exactly as doCommand() words them so an operator cannot
   tell which of the two paths produced the complaint.
*/
void XCopyCommandLine::cmdDiskInfo(const XCopyArgs &args)
{
    uint8_t firstCylinder = 0;
    uint8_t lastCylinder = MAX_CYLINDERS - 1;

    if (!parseCylinderRange(args.text("cyls"), firstCylinder, lastCylinder))
        return;

    // "both" and an absent option are the same thing. The table's choice list has
    // already refused anything that is not 0, 1 or both.
    int8_t side = -1;
    const String surface = args.text("side");
    if (surface == "0")
        side = 0;
    else if (surface == "1")
        side = 1;

    // "<first>-<last>,<side>[,<path>]", path last because a filename may contain a
    // comma and the numeric fields never can.
    const String range = String(firstCylinder) + "-" + String(lastCylinder) + "," + String(side);

    String filename = args.text("file");
    if (filename != "")
    {
        // On a copy: toLowerCase() mutates in place, and filename is the path to
        // open, which has to keep the case the user typed.
        String extension = filename;
        if (!extension.toLowerCase().endsWith(".scp"))
        {
            Log << F("The file must be an SCP file\r\n");
            return;
        }

        if (!mountSdCard())
            return;

        _callback(_caller, "diskInfoFile," + range + "," + filename);
        return;
    }

    if (!_floppy->diskChange())
    {
        Log << F("Disk not inserted into floppy\r\n");
        return;
    }

    _callback(_caller, "diskInfoScan," + range);
}

void XCopyCommandLine::cmdDriveToolkit()
{
    // Same pattern as cmdHeadCal(): start the state and return. The toolkit draws
    // its own table and takes the keyboard through the raw key hook, so owning the
    // console in a loop here would starve the ESP link and the TFT for as long as
    // somebody was poking at the drive.
    _callback(_caller, "driveToolkit");
}

void XCopyCommandLine::cmdName()
{
    Log << F("Diskname: ") << _floppy->getName() << F("\r\n");
}

void XCopyCommandLine::cmdPrint()
{
    _floppy->printTrack();
    Log << F("OK\r\n");
}

void XCopyCommandLine::cmdRead(const XCopyArgs &args)
{
    const int track = (int)args.subjectNumber(0);

    // "read <n> -flash" is what "readf <n>" was. Same eleven sectors, out of the
    // flash disk image instead of off the drive.
    if (args.has("flash"))
    {
        readTrackFromFlash((uint16_t)track);
        return;
    }

    Log.printf("Reading Track %2d:\r\n", track);
    _floppy->gotoLogicTrack(track);
    // int, not uint8_t: readTrack() signals failure with -1.
    int errors = _floppy->readTrack(false);
    if (errors != -1)
    {
        Log << F("Sectors found: ") << _floppy->getSectorCnt() << F(" Errors found: ");
        Log << String(errors, BIN);
        Log << F(" Track expected: ") + String(track) + F(" Track found: ") + String(_floppy->getTrackInfo()) + F(" bitCount: ") + String(_floppy->getBitCount()) + F(" (Read OK)\r\n");
    }
    else
    {
        Log << F("bitCount: ") + String(_floppy->getBitCount()) + F(" (Read failed!)\r\n");
    }
}

/*
   Open an image, describe it, and hand back the open device.

   Shared by "vol" and "dump", which differ only in whether they go on to list the
   root directory. Both open read only: neither changes anything, and an image
   opened read only cannot be damaged by a mistake in either.

   @result an open, mounted device the caller must adfDevClose(), or nullptr - in
           which case the reason has already been printed.
*/
struct AdfDevice *XCopyCommandLine::openImageForReading(const String &path)
{
    XCopyAdf::begin();
    XCopyAdf::clearErrors();

    // adfDevOpenWithDriver rather than adfDevOpen: the driver that can read a file
    // off the card is known here, and letting the library guess from the path would
    // only give it a chance to guess wrong.
    struct AdfDevice *dev = adfDevOpenWithDriver("sd", path.c_str(),
                                                 ADF_ACCESS_MODE_READONLY);
    if (dev == NULL)
    {
        Log << XCopyConsole::error("unable to open '" + path + "'") << F("\r\n");
        return nullptr;
    }

    XCopyAdfView::printDevice(dev);

    if (adfDevMount(dev) != ADF_RC_OK)
    {
        // A device that will not mount is still worth describing, which is why
        // printDevice() ran first: "1760 blocks, unknown type" answers most of the
        // questions somebody asks of a file that will not open.
        Log << XCopyConsole::error("no filesystem found on '" + path + "'") << F("\r\n");
        adfDevClose(dev);
        return nullptr;
    }

    return dev;
}

void XCopyCommandLine::cmdVol(const XCopyArgs &args)
{
    /*
       Either a slot that is already mounted, or a file to open just for this.
       "vol ADF0:" asks about what is in a slot, which is the question anyone with
       something mounted is actually asking; "vol game.adf" asks about a file
       without disturbing the table.
    */
    XCopyPath named;
    if (xcopySplitPath(args.subject(), named) && named.qualified && !named.isCard())
    {
        XCopyAdfMount::Slot *slot = XCopyAdfMount::find(named.device);
        if (slot == nullptr || !slot->mounted())
        {
            Log << XCopyConsole::error(named.device + ": has nothing mounted") << F("\r\n");
            return;
        }

        XCopyAdfView::printDevice(slot->dev);
        XCopyAdfView::printVolume(slot->vol);
        return;
    }

    const String path = args.subject();

    struct AdfDevice *dev = openImageForReading(path);
    if (dev == nullptr)
        return;

    for (int i = 0; i < dev->nVol; i++)
    {
        struct AdfVolume *vol = adfVolMount(dev, i, ADF_ACCESS_MODE_READONLY);
        if (vol == NULL)
        {
            Log << XCopyConsole::error("unable to mount volume " + String(i)) << F("\r\n");
            continue;
        }

        XCopyAdfView::printVolume(vol);
        adfVolUnMount(vol);
    }

    adfDevClose(dev);
}

void XCopyCommandLine::cmdDump(const XCopyArgs &args)
{
    const String path = args.subject();

    struct AdfDevice *dev = openImageForReading(path);
    if (dev == nullptr)
        return;

    for (int i = 0; i < dev->nVol; i++)
    {
        struct AdfVolume *vol = adfVolMount(dev, i, ADF_ACCESS_MODE_READONLY);
        if (vol == NULL)
        {
            Log << XCopyConsole::error("unable to mount volume " + String(i)) << F("\r\n");
            continue;
        }

        XCopyAdfView::printVolume(vol);
        Log << F("Directory:\r\n");
        XCopyAdfView::printListHeader();

        const uint16_t listed = XCopyAdfView::printDirectory(vol, vol->rootBlock);
        Log << listed << (listed == 1 ? F(" entry\r\n") : F(" entries\r\n"));

        adfVolUnMount(vol);
    }

    adfDevClose(dev);
}

void XCopyCommandLine::cmdWeak()
{
    Log << _floppy->getWeakTrack() << F("\r\n");
}

// DATE AND TIME
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
